signalben/Planar-Grasping-Platform/scara_CAD/endstops/amount.SLDPRT

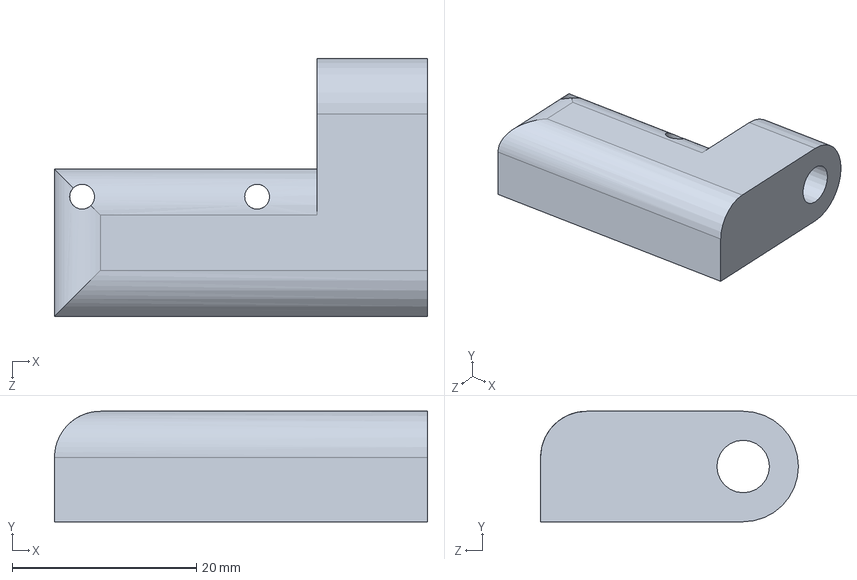
[picture p21: CAD file, 2021-09-22]
scara_CAD/endstops/amount.SLDPRT
40.5 x 12.0 x 28.0 mm
