signalben/Planar-Grasping-Platform/scara_CAD/gripper/top_plate2.SLDPRT

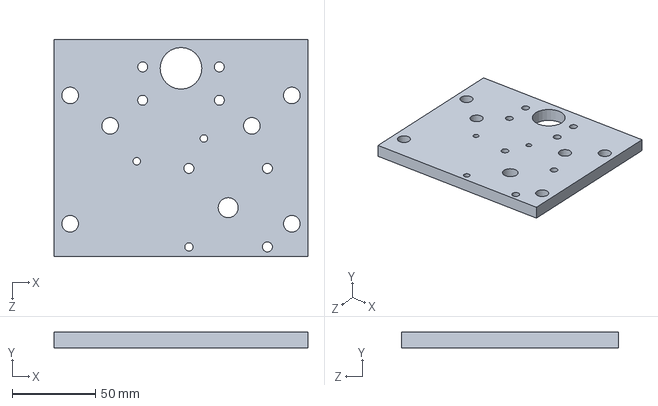
[picture p22: CAD file, 2021-09-22]
scara_CAD/gripper/top_plate2.SLDPRT
152.4 x 9.50 x 130.0 mm
