signalben/Planar-Grasping-Platform/scara_CAD/realsenseD415_mount/camera_end.SLDPRT

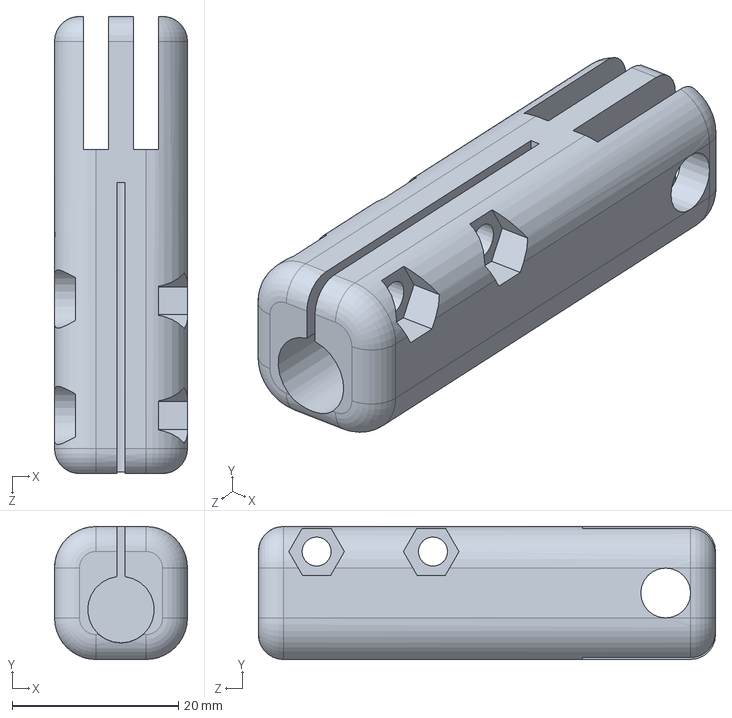
[picture p23: CAD file, 2021-09-22]
scara_CAD/realsenseD415_mount/camera_end.SLDPRT
16.0 x 16.0 x 55.0 mm
