signalben/Planar-Grasping-Platform/scara_ws/src/scara_description/ZL.STL

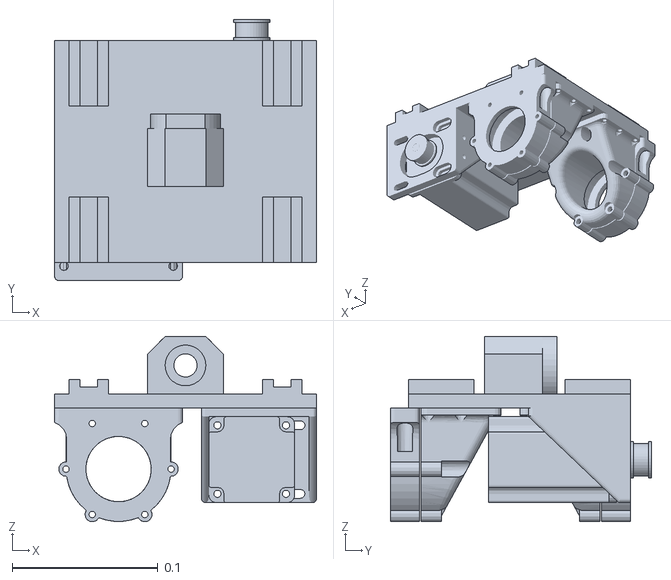
[picture p24: CAD file, 2021-09-26]
scara_ws/src/scara_description/ZL.STL
0.18 x 0.179 x 0.127
