signalben/Planar-Grasping-Platform/scara_CAD/controller/mega holder.SLDPRT

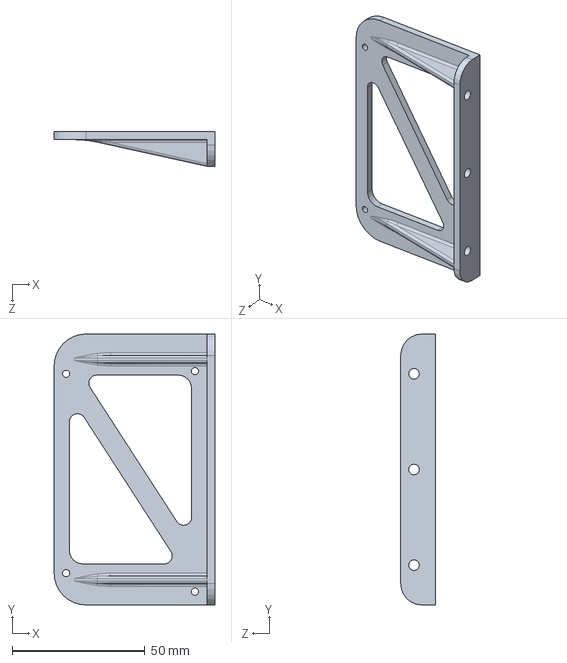
[picture p25: CAD file, 2021-09-22]
scara_CAD/controller/mega holder.SLDPRT
60.5 x 102.0 x 13.0 mm
