signalben/Planar-Grasping-Platform/scara_CAD/endstops/zmount#.SLDPRT

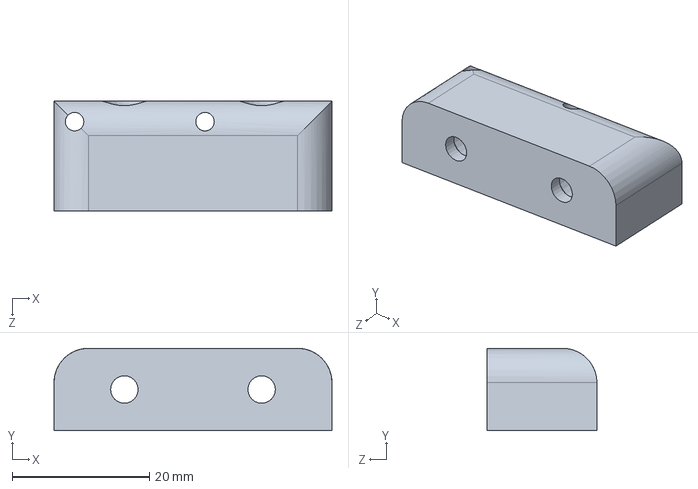
[picture p26: CAD file, 2021-09-22]
scara_CAD/endstops/zmount#.SLDPRT
40.5 x 12.0 x 16.0 mm
