signalben/Planar-Grasping-Platform/scara_CAD/gripper/motor.SLDPRT

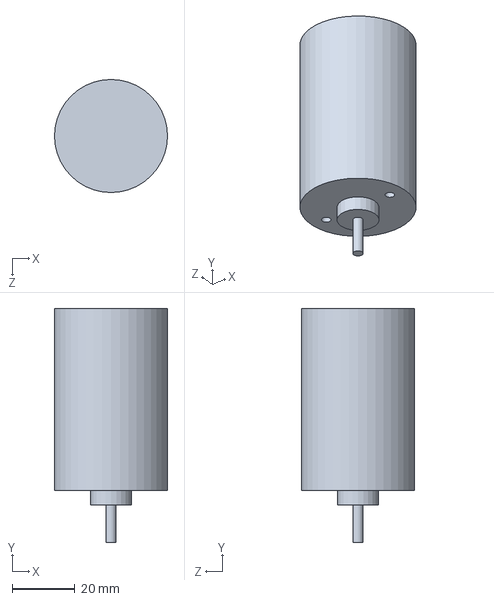
[picture p27: CAD file, 2021-09-22]
scara_CAD/gripper/motor.SLDPRT
36.0 x 74.5 x 36.0 mm
