signalben/Planar-Grasping-Platform/scara_CAD/manipulator/nema17_mount.SLDPRT

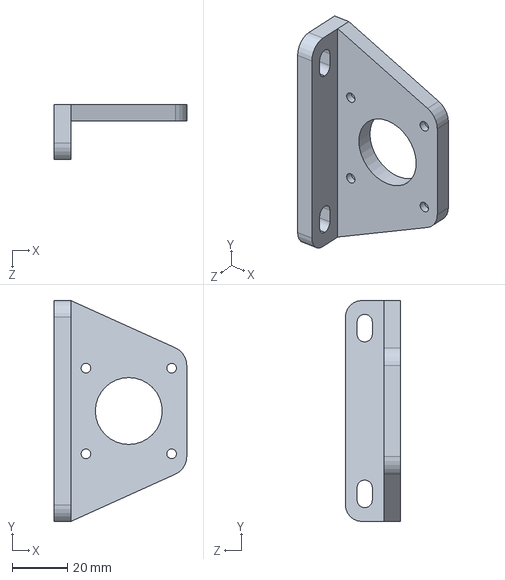
[picture p28: CAD file, 2021-09-22]
scara_CAD/manipulator/nema17_mount.SLDPRT
48.0 x 80.0 x 20.0 mm
