signalben/Planar-Grasping-Platform/scara_CAD/realsenseD415_mount/camera_rod.SLDPRT

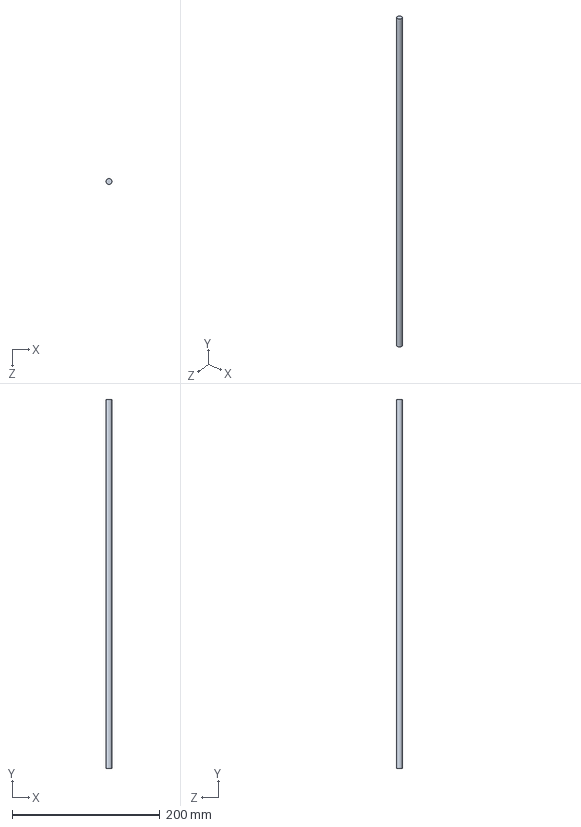
[picture p29: CAD file, 2021-09-22]
scara_CAD/realsenseD415_mount/camera_rod.SLDPRT
8.00 x 500.0 x 8.00 mm
