signalben/Planar-Grasping-Platform/scara_ws/src/scara_description/YL.STL

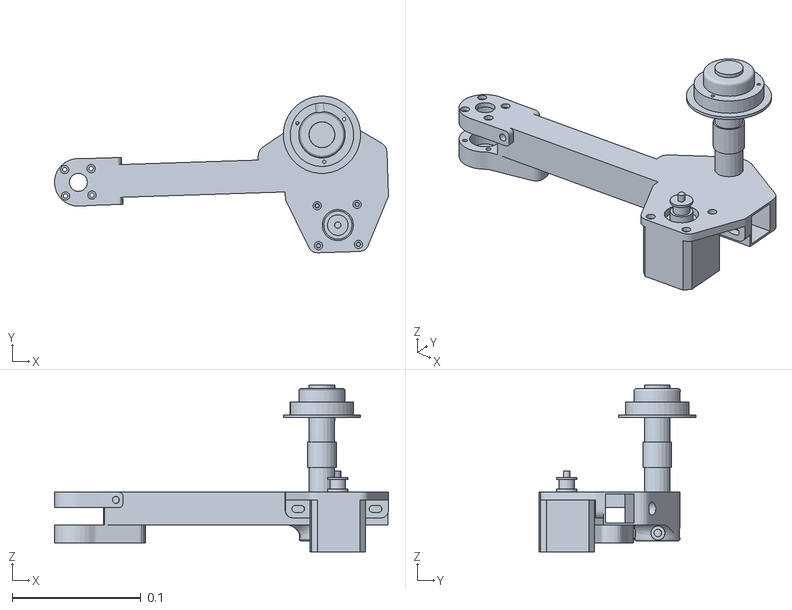
[picture p30: CAD file, 2021-09-26]
scara_ws/src/scara_description/YL.STL
0.259 x 0.121 x 0.129
