signalben/Planar-Grasping-Platform/scara_CAD/controller/fan_plate.SLDPRT

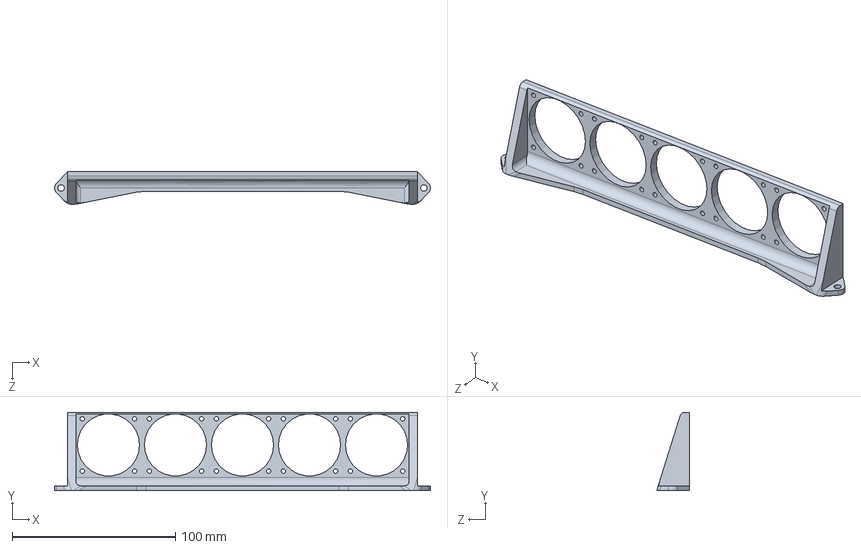
[picture p31: CAD file, 2021-09-22]
scara_CAD/controller/fan_plate.SLDPRT
230.0 x 48.0 x 20.0 mm
