signalben/Planar-Grasping-Platform/scara_CAD/endstops/amount2.SLDPRT

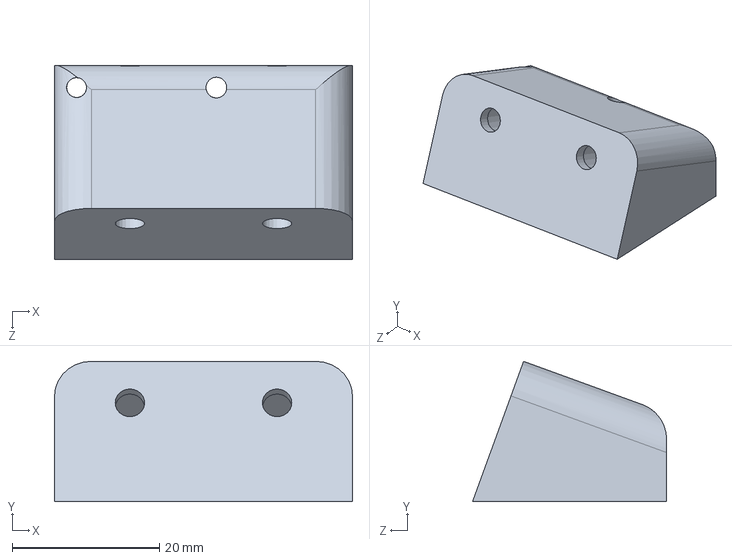
[picture p32: CAD file, 2021-09-22]
scara_CAD/endstops/amount2.SLDPRT
40.5 x 19.1 x 26.4 mm
