signalben/Planar-Grasping-Platform/scara_CAD/gripper/small_side_plate.SLDPRT

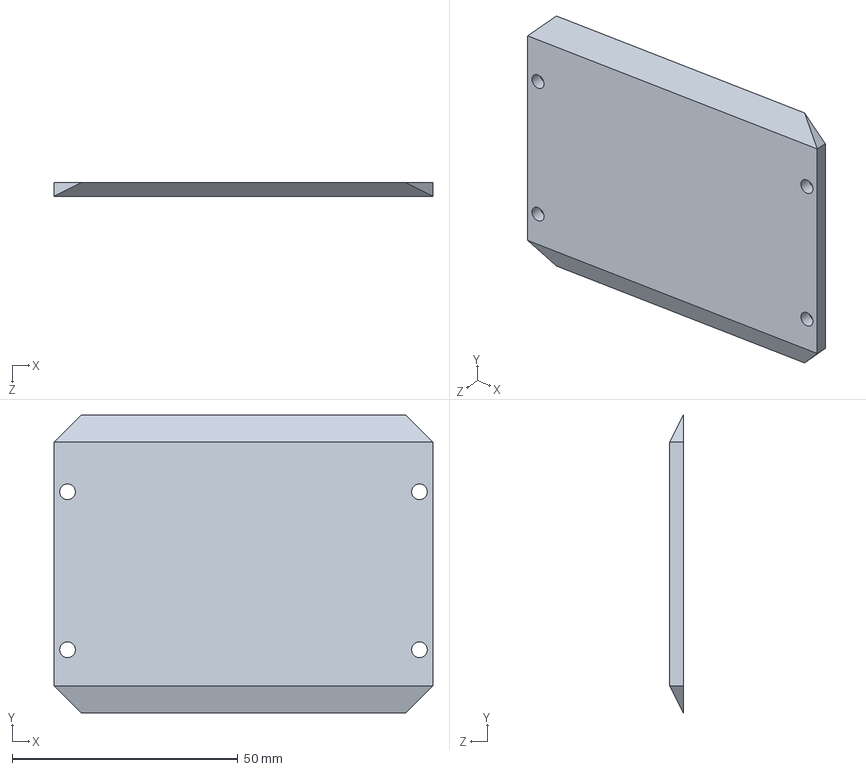
[picture p33: CAD file, 2021-09-22]
scara_CAD/gripper/small_side_plate.SLDPRT
84.0 x 66.0 x 3.00 mm
