signalben/Planar-Grasping-Platform/scara_CAD/manipulator/ballnut_holder.SLDPRT

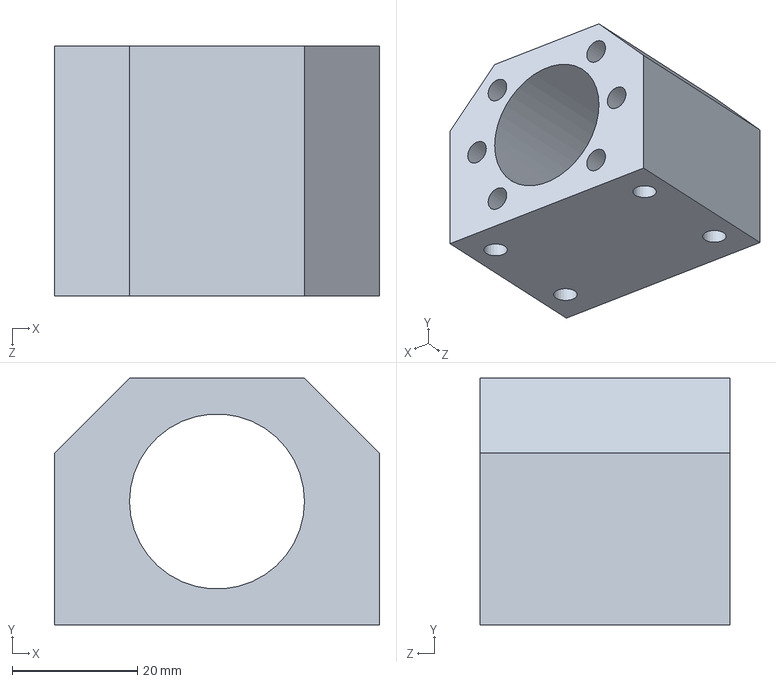
[picture p34: CAD file, 2021-09-22]
scara_CAD/manipulator/ballnut_holder.SLDPRT
52.0 x 39.5 x 40.0 mm
