signalben/Planar-Grasping-Platform/scara_ws/src/scara_description/jaw1.STL

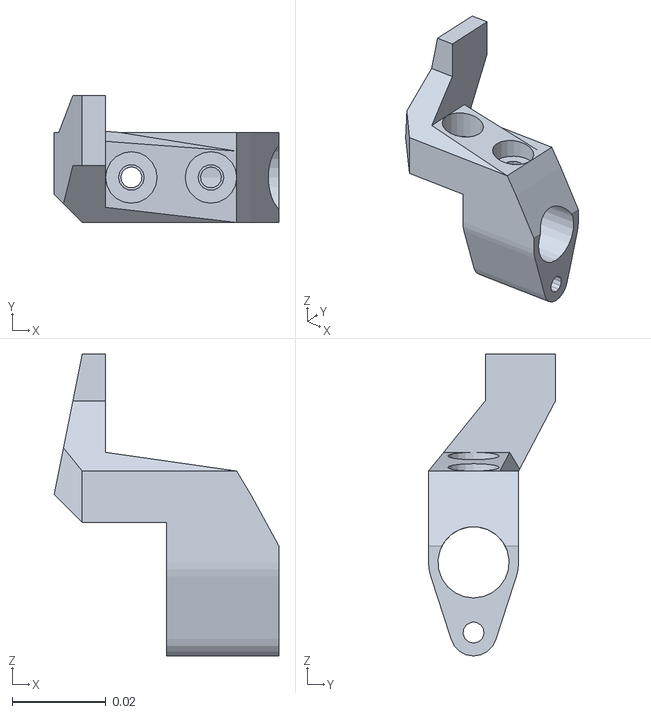
[picture p35: CAD file, 2021-09-26]
scara_ws/src/scara_description/jaw1.STL
0.048 x 0.0271 x 0.0645
