signalben/Planar-Grasping-Platform/scara_CAD/controller/clamp.SLDPRT

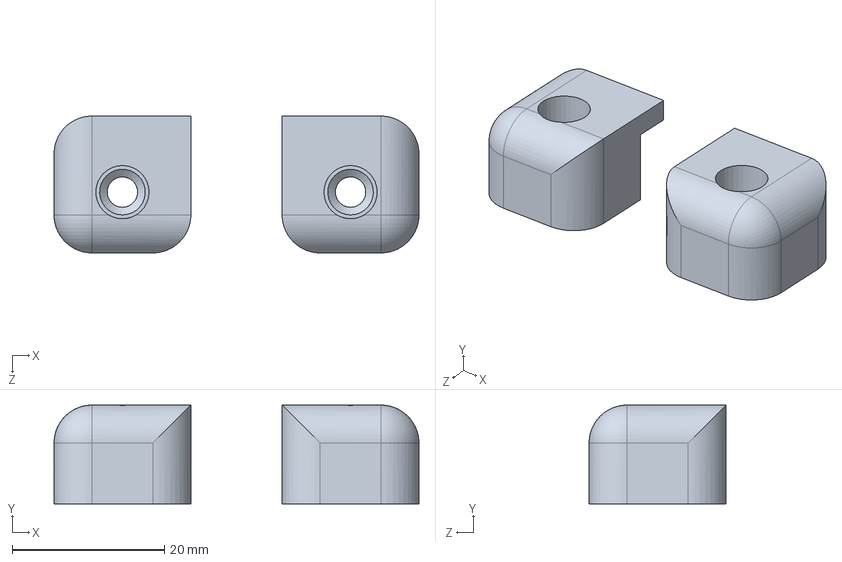
[picture p36: CAD file, 2021-09-22]
scara_CAD/controller/clamp.SLDPRT
48.0 x 13.0 x 18.0 mm
