signalben/Planar-Grasping-Platform/scara_CAD/endstops/bmount.SLDPRT

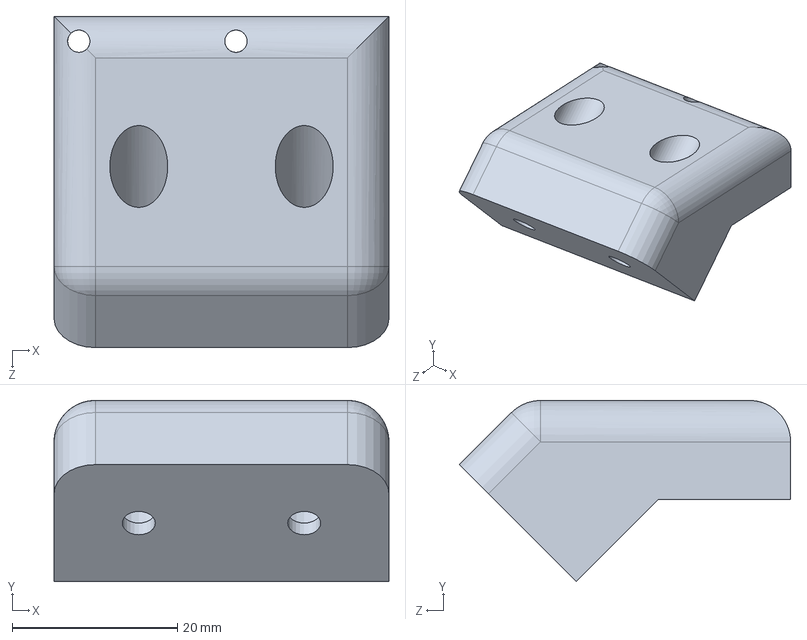
[picture p37: CAD file, 2021-09-22]
scara_CAD/endstops/bmount.SLDPRT
40.5 x 21.9 x 40.0 mm
