signalben/Planar-Grasping-Platform/scara_CAD/gripper/finger.SLDPRT

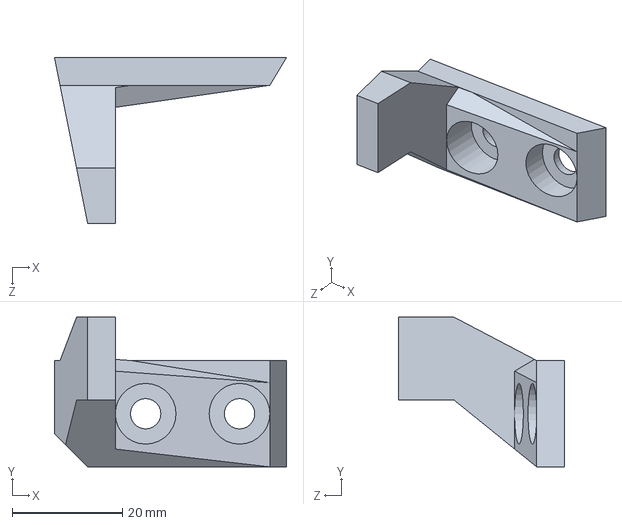
[picture p38: CAD file, 2021-09-22]
scara_CAD/gripper/finger.SLDPRT
42.0 x 27.1 x 30.0 mm
