signalben/Planar-Grasping-Platform/scara_CAD/manipulator/gt2_25t.SLDPRT

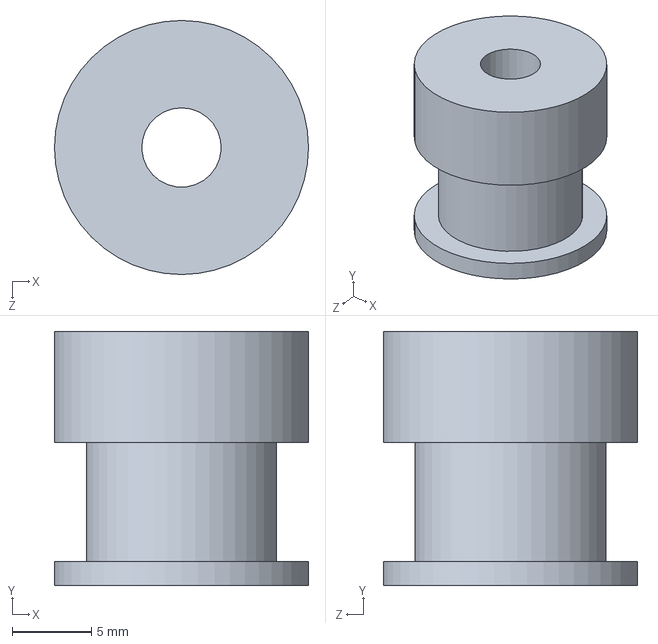
[picture p39: CAD file, 2021-09-22]
scara_CAD/manipulator/gt2_25t.SLDPRT
16.0 x 16.0 x 16.0 mm
