signalben/Planar-Grasping-Platform/scara_CAD/realsenseD415_mount/sidemount.SLDPRT

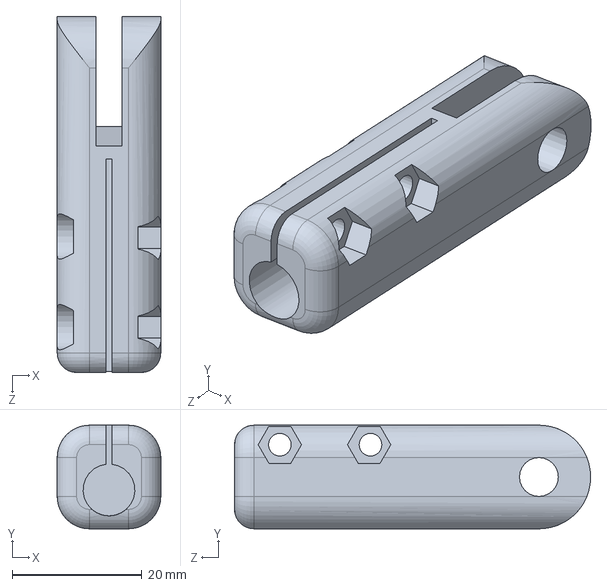
[picture p40: CAD file, 2021-09-22]
scara_CAD/realsenseD415_mount/sidemount.SLDPRT
16.0 x 16.0 x 55.0 mm
