signalben/Planar-Grasping-Platform/scara_ws/src/scara_description/XL.STL

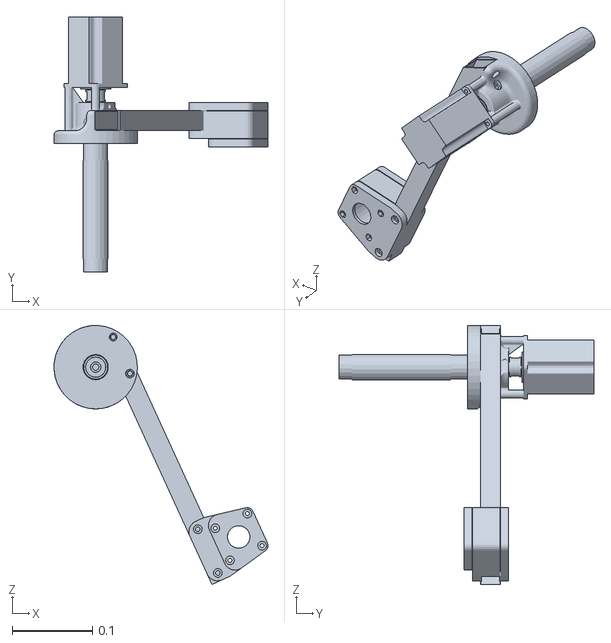
[picture p41: CAD file, 2021-09-26]
scara_ws/src/scara_description/XL.STL
0.267 x 0.317 x 0.323
