signalben/Planar-Grasping-Platform/scara_CAD/gripper/shell_no_motor.SLDPRT

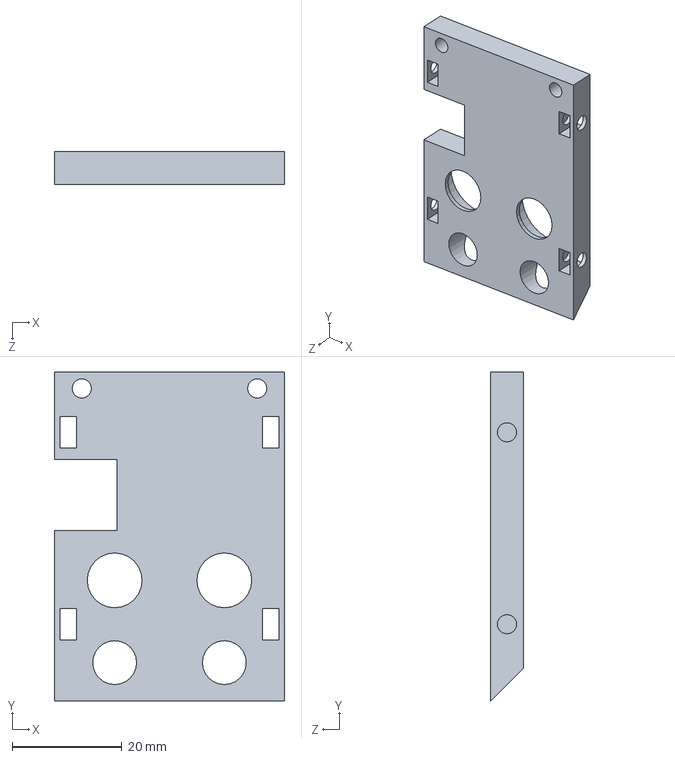
[picture p43: CAD file, 2021-09-22]
scara_CAD/gripper/shell_no_motor.SLDPRT
42.0 x 60.0 x 6.00 mm
