signalben/Planar-Grasping-Platform/scara_CAD/manipulator/side_plate.SLDPRT

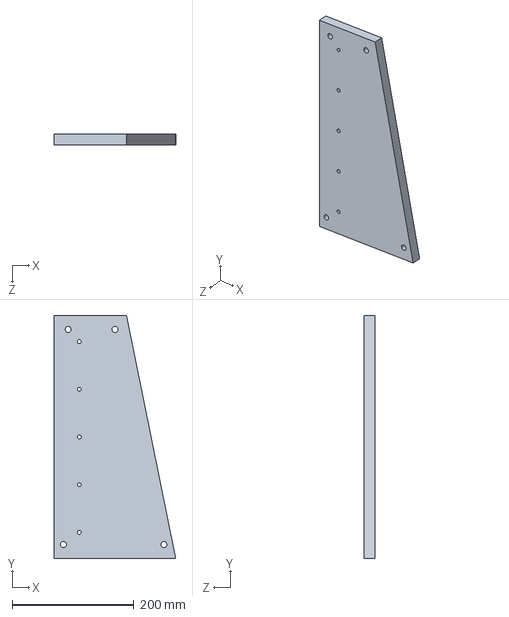
[picture p44: CAD file, 2021-09-22]
scara_CAD/manipulator/side_plate.SLDPRT
200.0 x 400.0 x 18.0 mm
