signalben/Planar-Grasping-Platform/scara_CAD/realsenseD415_mount/sidemount2.SLDPRT

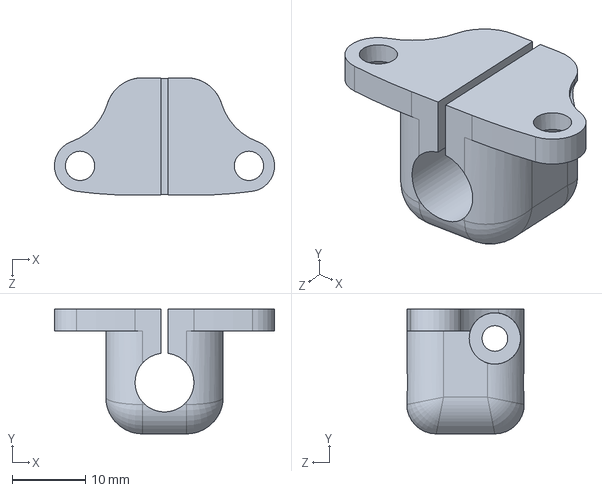
[picture p45: CAD file, 2021-09-22]
scara_CAD/realsenseD415_mount/sidemount2.SLDPRT
30.0 x 17.0 x 16.0 mm
