signalben/Planar-Grasping-Platform/scara_ws/src/scara_description/AL.STL

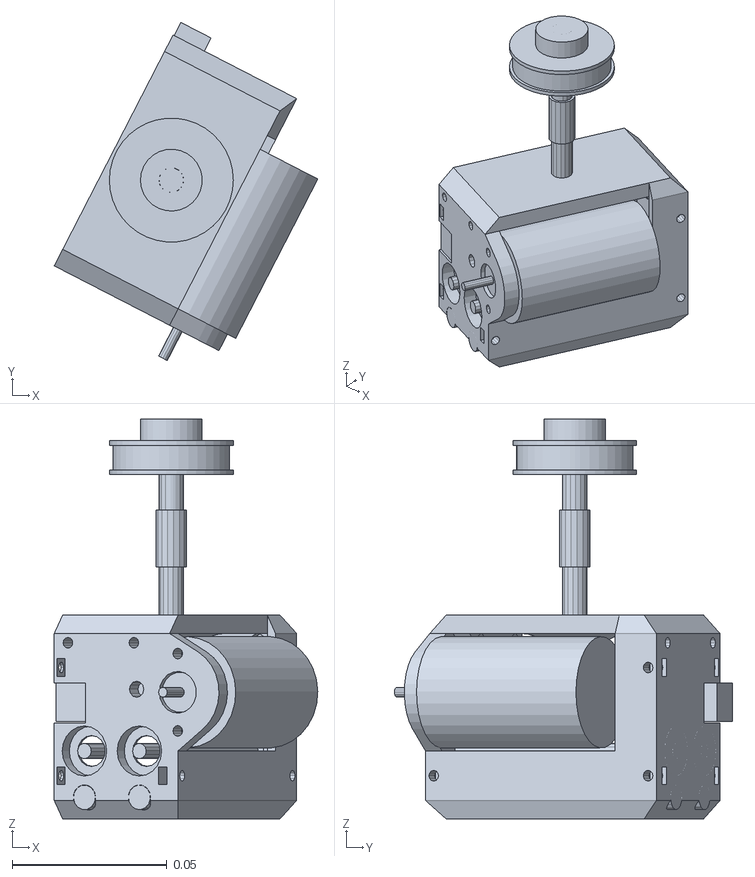
[picture p46: CAD file, 2021-09-26]
scara_ws/src/scara_description/AL.STL
0.0853 x 0.109 x 0.129
