signalben/Planar-Grasping-Platform/scara_CAD/gripper/mini_bearing.SLDPRT

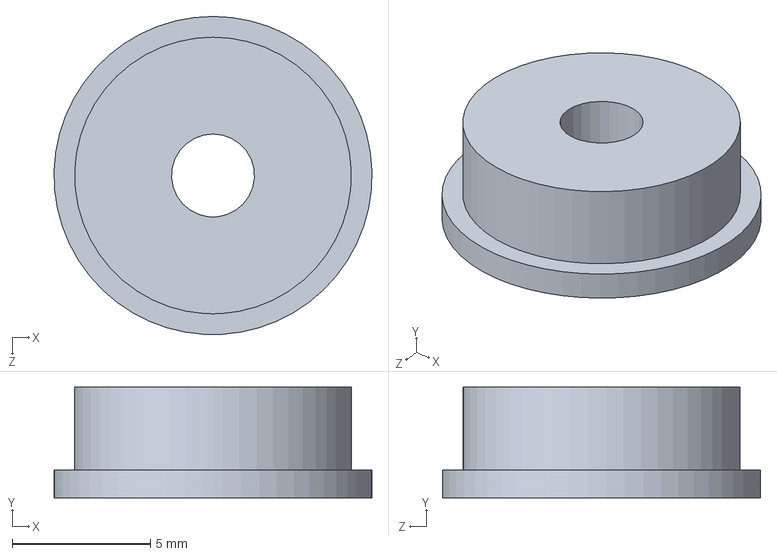
[picture p47: CAD file, 2021-09-22]
scara_CAD/gripper/mini_bearing.SLDPRT
11.5 x 4.00 x 11.5 mm
