signalben/Planar-Grasping-Platform/scara_CAD/manipulator/large_bearing.SLDPRT

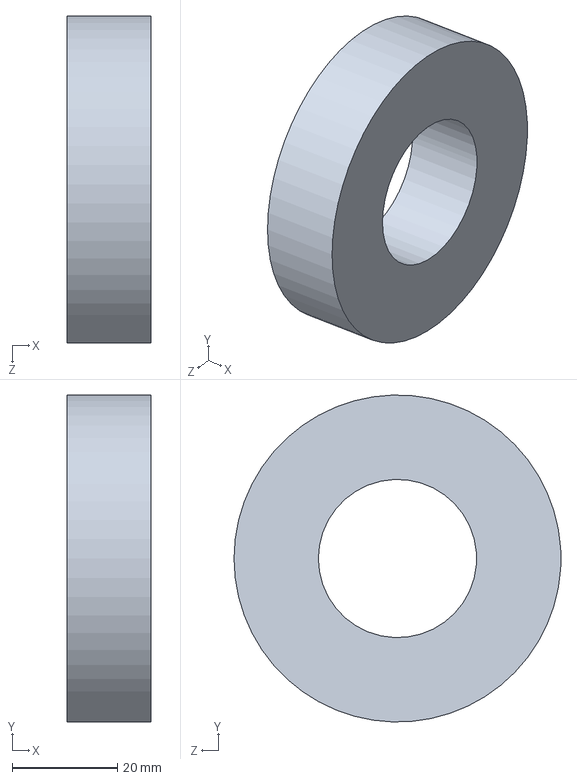
[picture p48: CAD file, 2021-09-22]
scara_CAD/manipulator/large_bearing.SLDPRT
16.0 x 62.0 x 62.0 mm
