signalben/Planar-Grasping-Platform/scara_CAD/gripper/gear1.SLDPRT

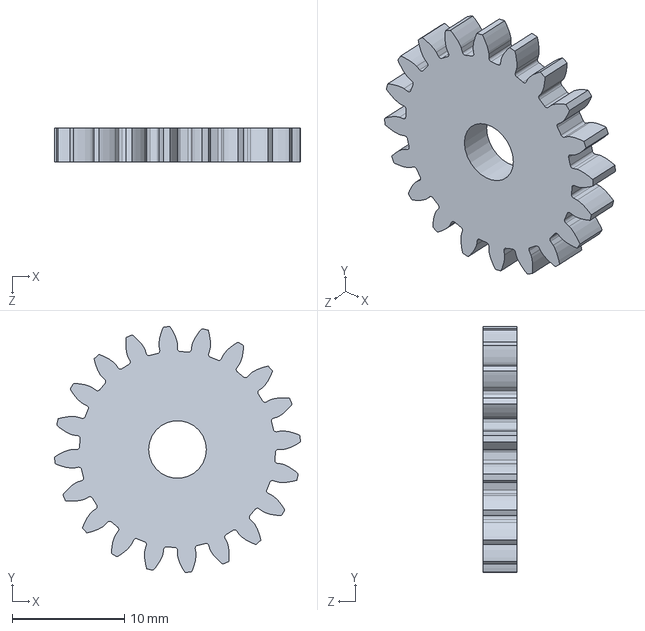
[picture p49: CAD file, 2021-09-22]
scara_CAD/gripper/gear1.SLDPRT
22.0 x 22.0 x 3.00 mm
