signalben/Planar-Grasping-Platform/scara_CAD/manipulator/new_tensioner.SLDPRT

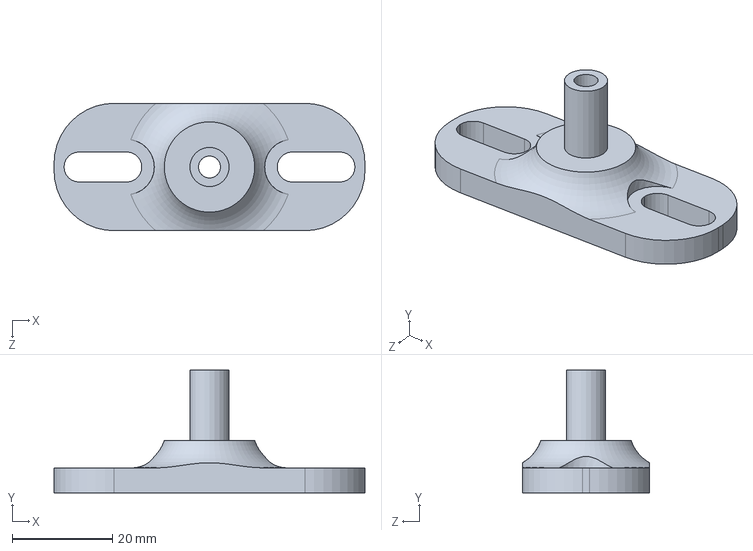
[picture p50: CAD file, 2021-09-22]
scara_CAD/manipulator/new_tensioner.SLDPRT
62.0 x 24.5 x 25.4 mm
