signalben/Planar-Grasping-Platform/scara_CAD/gripper/potentiomer.SLDPRT

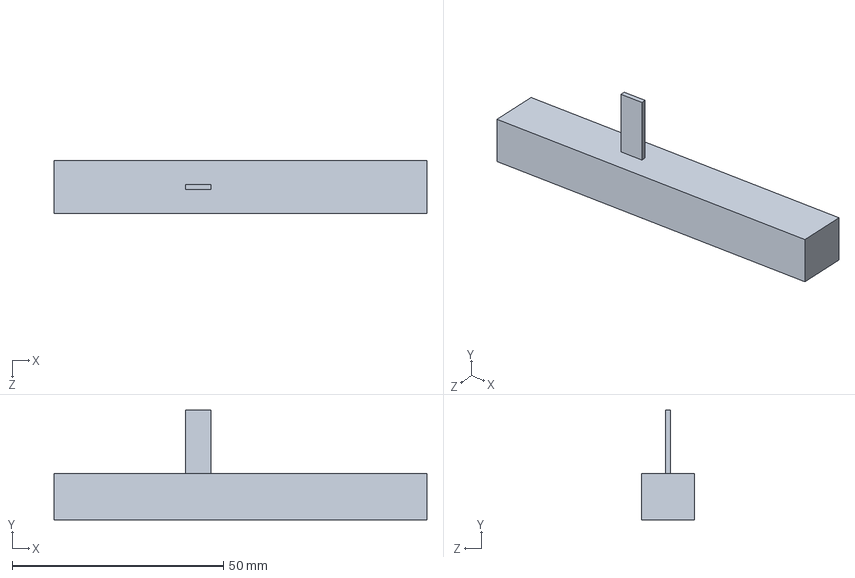
[picture p51: CAD file, 2021-09-22]
scara_CAD/gripper/potentiomer.SLDPRT
88.2 x 26.0 x 12.5 mm
