signalben/Planar-Grasping-Platform/scara_CAD/manipulator/j2_tensioner.SLDPRT

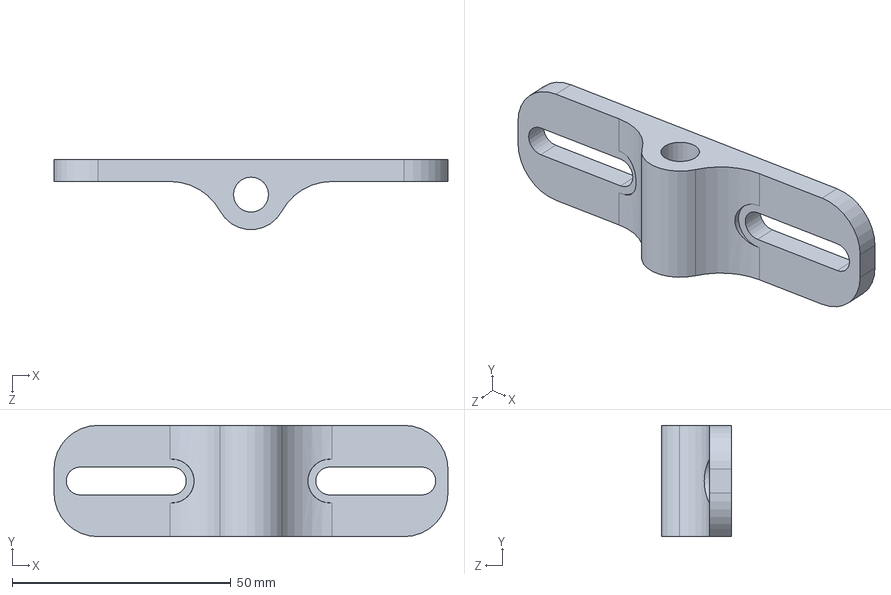
[picture p52: CAD file, 2021-09-22]
scara_CAD/manipulator/j2_tensioner.SLDPRT
90.0 x 25.4 x 15.9 mm
