signalben/Planar-Grasping-Platform/scara_CAD/gripper/skate_bearing2.SLDPRT

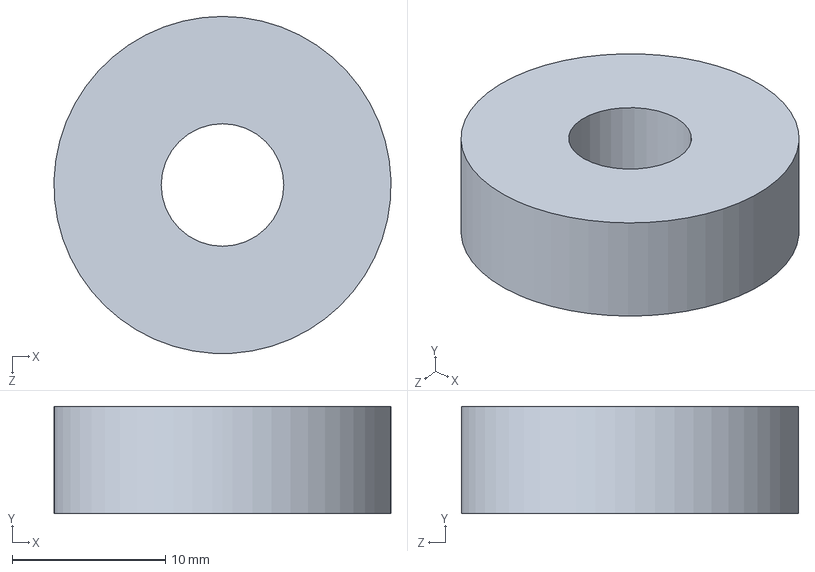
[picture p53: CAD file, 2021-09-22]
scara_CAD/gripper/skate_bearing2.SLDPRT
22.0 x 7.00 x 22.0 mm
