signalben/Planar-Grasping-Platform/scara_CAD/manipulator/back_plate.SLDPRT

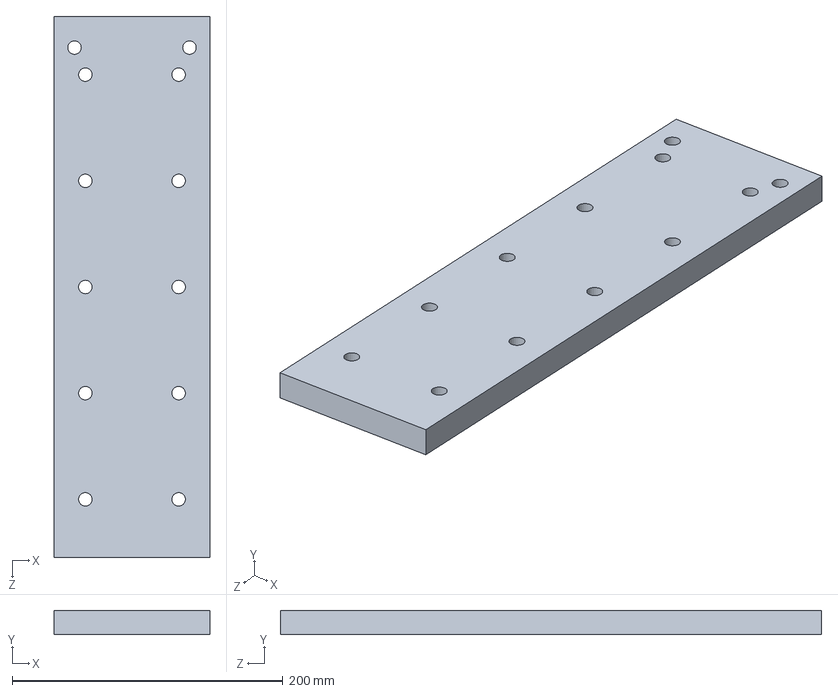
[picture p54: CAD file, 2021-09-22]
scara_CAD/manipulator/back_plate.SLDPRT
115.0 x 18.0 x 400.0 mm
