signalben/Planar-Grasping-Platform/scara_CAD/gripper/shell.SLDPRT

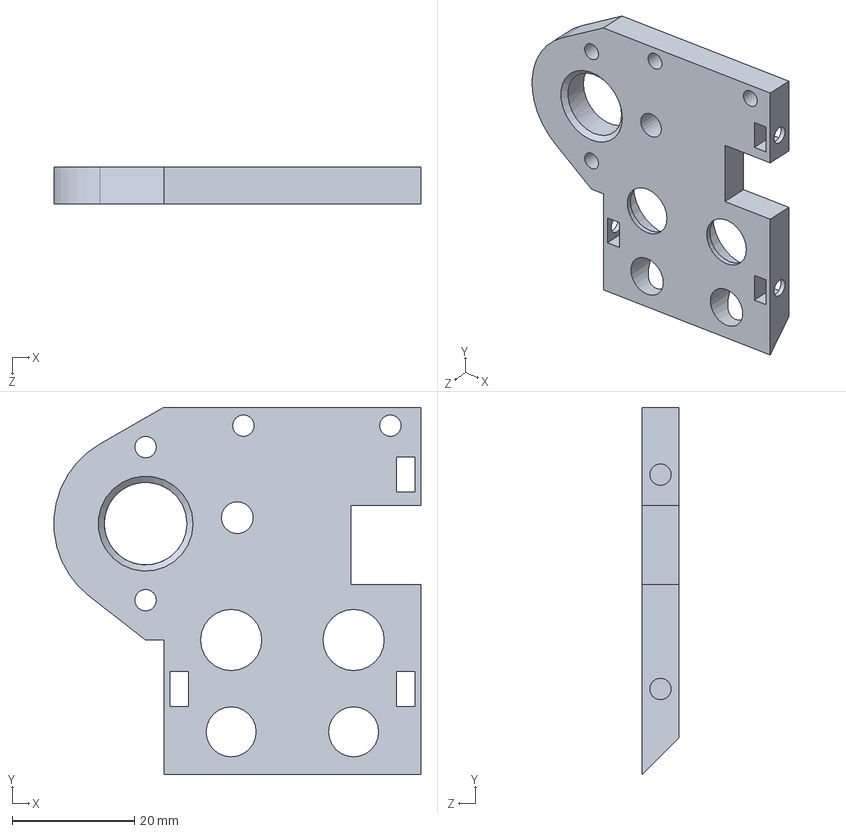
[picture p55: CAD file, 2021-09-22]
scara_CAD/gripper/shell.SLDPRT
59.9 x 60.0 x 6.00 mm
