signalben/Planar-Grasping-Platform/scara_CAD/manipulator/z_motor_mount.SLDPRT

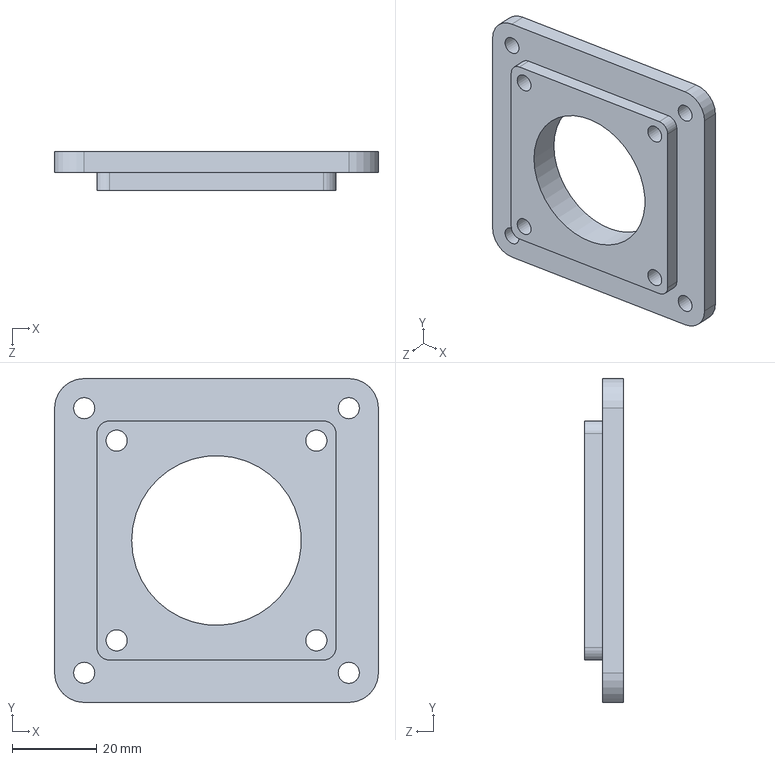
[picture p56: CAD file, 2021-09-22]
scara_CAD/manipulator/z_motor_mount.SLDPRT
76.4 x 76.4 x 9.20 mm
