signalben/Planar-Grasping-Platform/scara_CAD/gripper/rod.SLDPRT

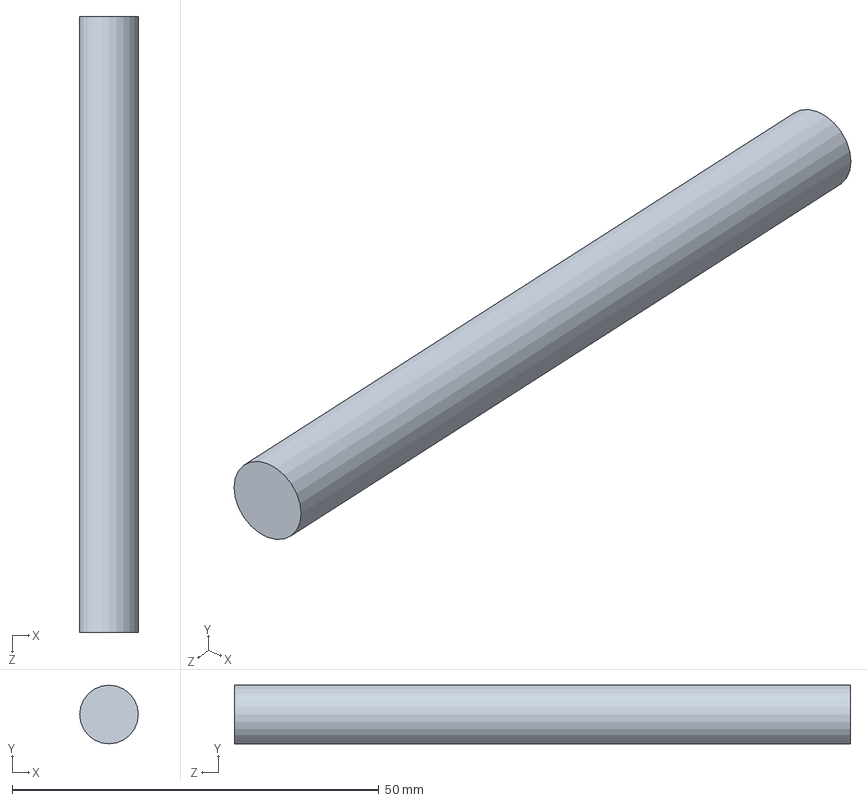
[picture p57: CAD file, 2021-09-22]
scara_CAD/gripper/rod.SLDPRT
8.00 x 8.00 x 84.0 mm
