signalben/Planar-Grasping-Platform/scara_CAD/manipulator/new2_tensioner.SLDPRT

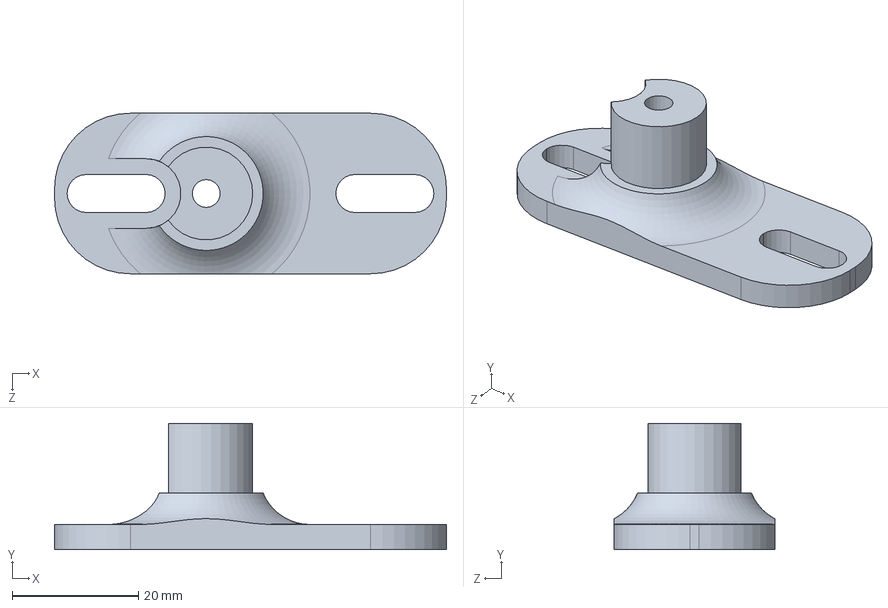
[picture p58: CAD file, 2021-09-22]
scara_CAD/manipulator/new2_tensioner.SLDPRT
62.0 x 20.0 x 25.4 mm
