signalben/Planar-Grasping-Platform/scara_CAD/gripper/mgear.SLDPRT

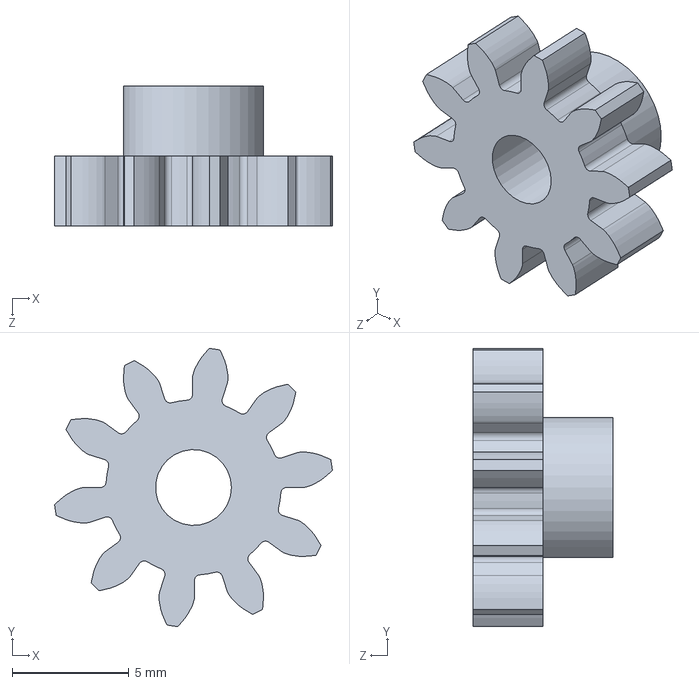
[picture p59: CAD file, 2021-09-22]
scara_CAD/gripper/mgear.SLDPRT
11.9 x 11.9 x 6.00 mm
