signalben/Planar-Grasping-Platform/scara_CAD/gripper/igear.SLDPRT

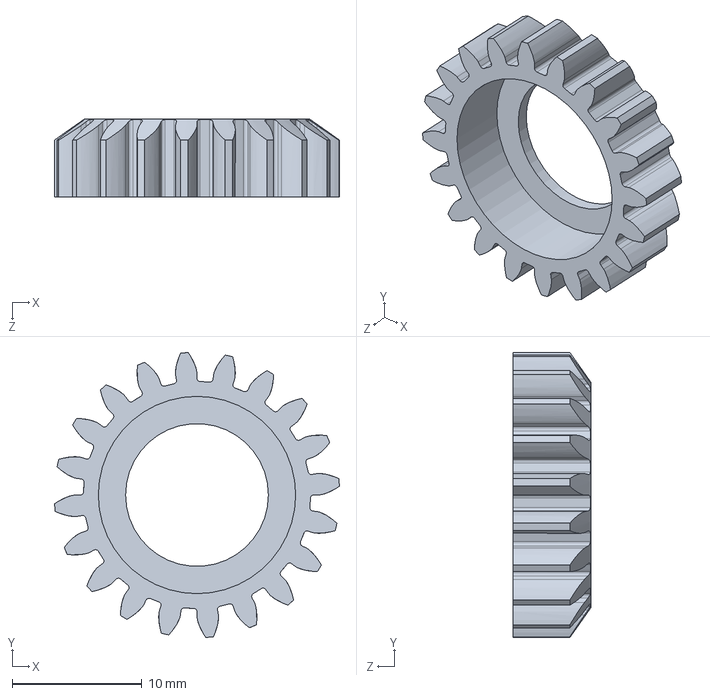
[picture p60: CAD file, 2021-09-22]
scara_CAD/gripper/igear.SLDPRT
22.0 x 22.0 x 6.00 mm
