signalben/Planar-Grasping-Platform/scara_CAD/manipulator/motot_mount_1.SLDPRT

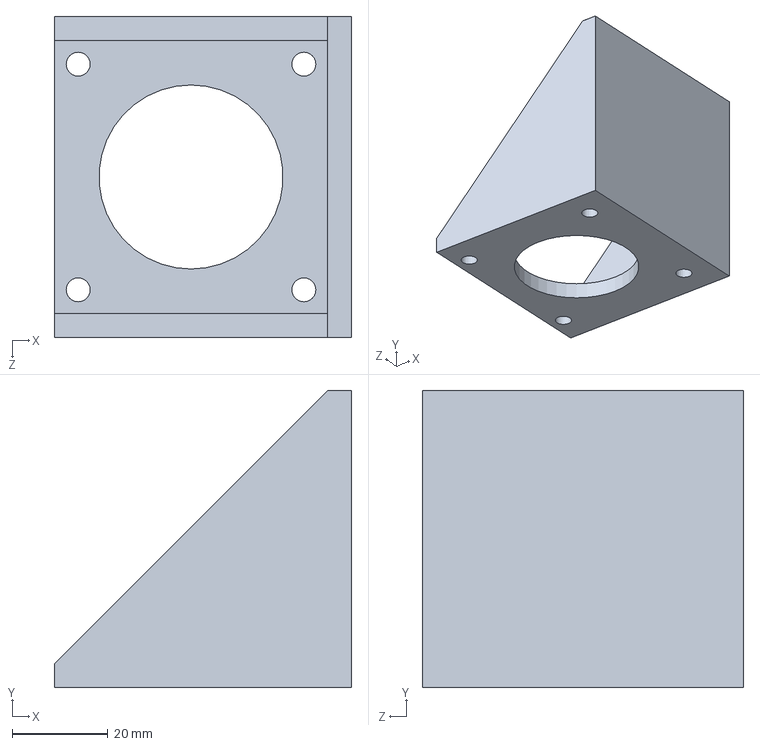
[picture p62: CAD file, 2021-09-22]
scara_CAD/manipulator/motot_mount_1.SLDPRT
62.0 x 62.0 x 67.0 mm
