signalben/Planar-Grasping-Platform/scara_CAD/manipulator/htd-22-15.SLDPRT

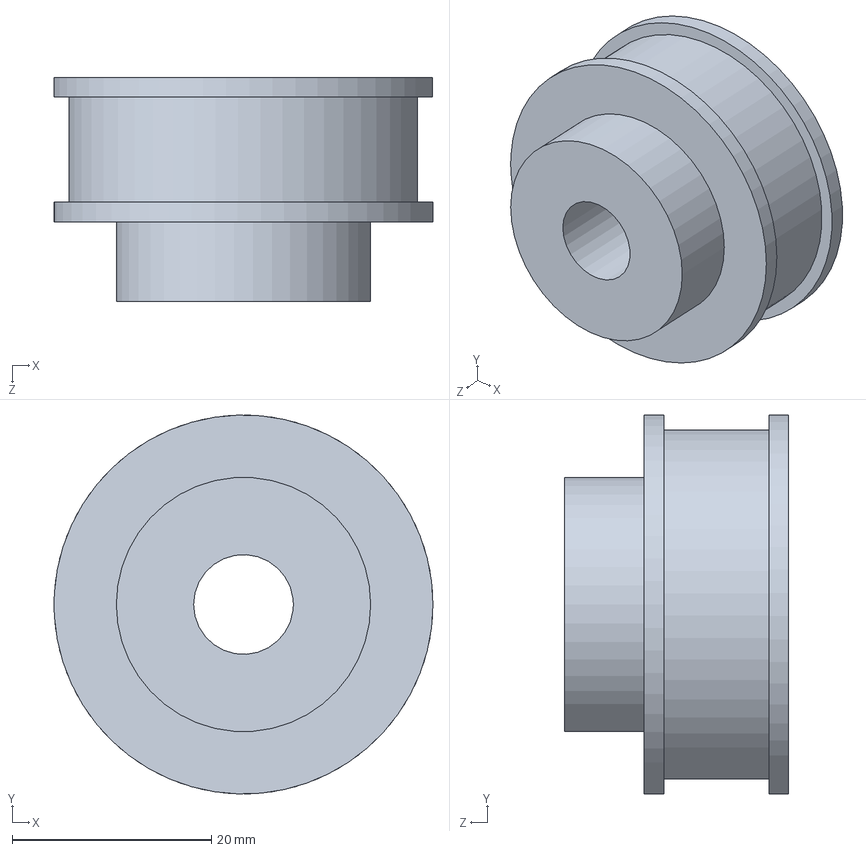
[picture p63: CAD file, 2021-09-22]
scara_CAD/manipulator/htd-22-15.SLDPRT
38.0 x 38.0 x 22.5 mm
