signalben/Planar-Grasping-Platform/scara_CAD/gripper/jaw.SLDPRT

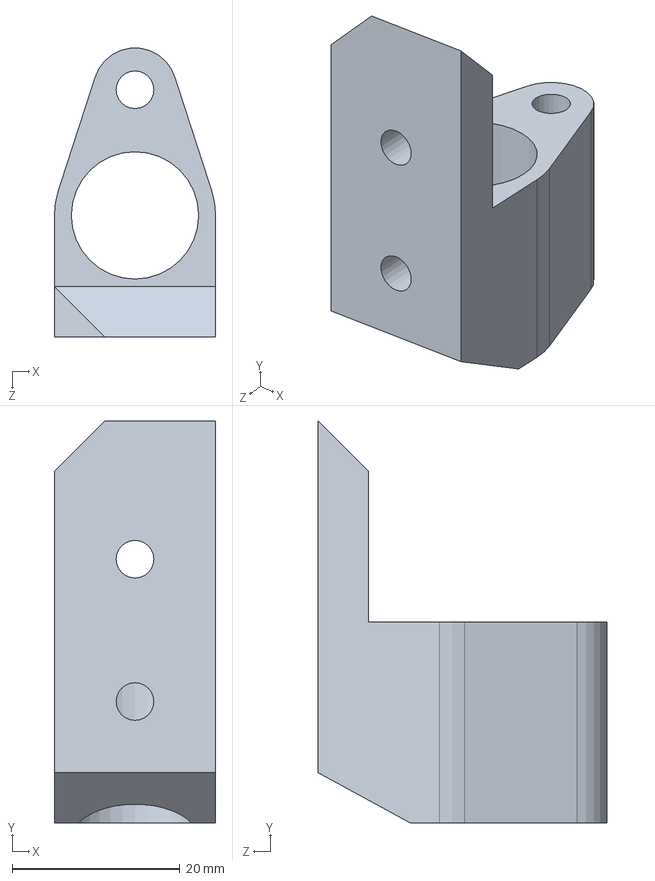
[picture p64: CAD file, 2021-09-22]
scara_CAD/gripper/jaw.SLDPRT
19.2 x 48.0 x 34.5 mm
