signalben/Planar-Grasping-Platform/scara_CAD/gripper/bearing6mm.SLDPRT

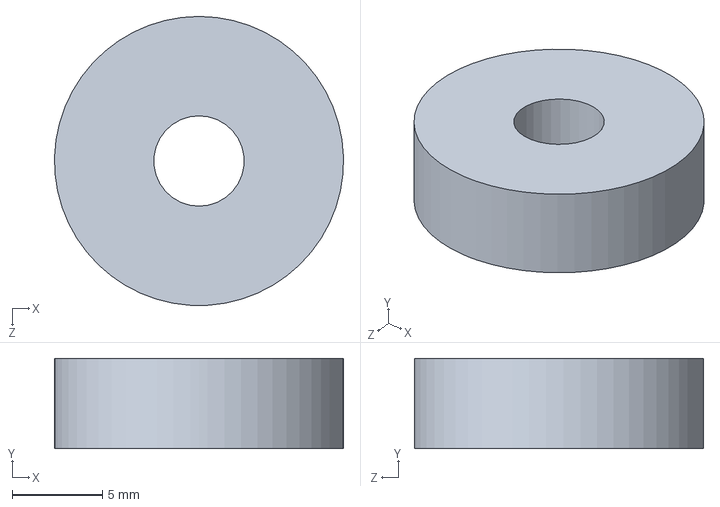
[picture p65: CAD file, 2021-09-22]
scara_CAD/gripper/bearing6mm.SLDPRT
16.0 x 5.00 x 16.0 mm
