signalben/Planar-Grasping-Platform/scara_CAD/gripper/top.SLDPRT

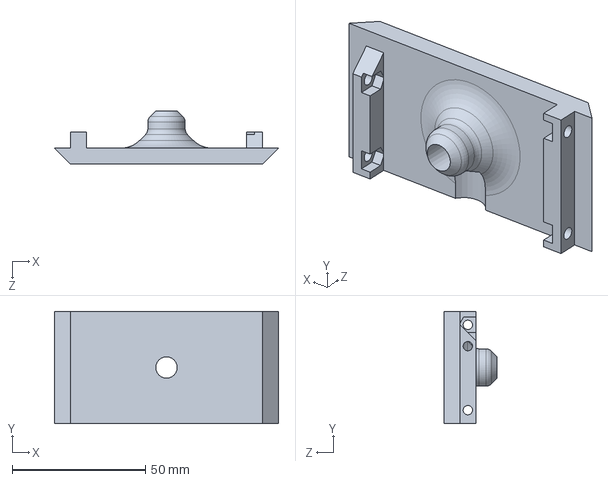
[picture p66: CAD file, 2021-09-22]
scara_CAD/gripper/top.SLDPRT
84.0 x 42.0 x 20.0 mm
