signalben/Planar-Grasping-Platform/scara_CAD/manipulator/joint2.SLDPRT

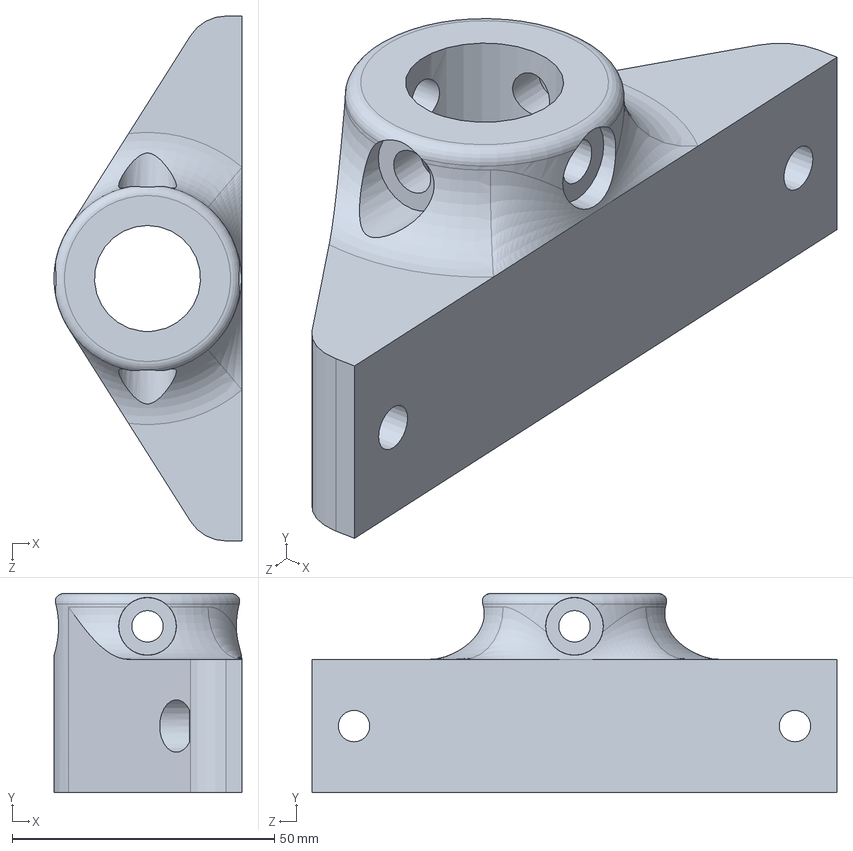
[picture p67: CAD file, 2021-09-22]
scara_CAD/manipulator/joint2.SLDPRT
35.8 x 38.0 x 100.0 mm
