signalben/Planar-Grasping-Platform/scara_CAD/gripper/linear_bearing.SLDPRT

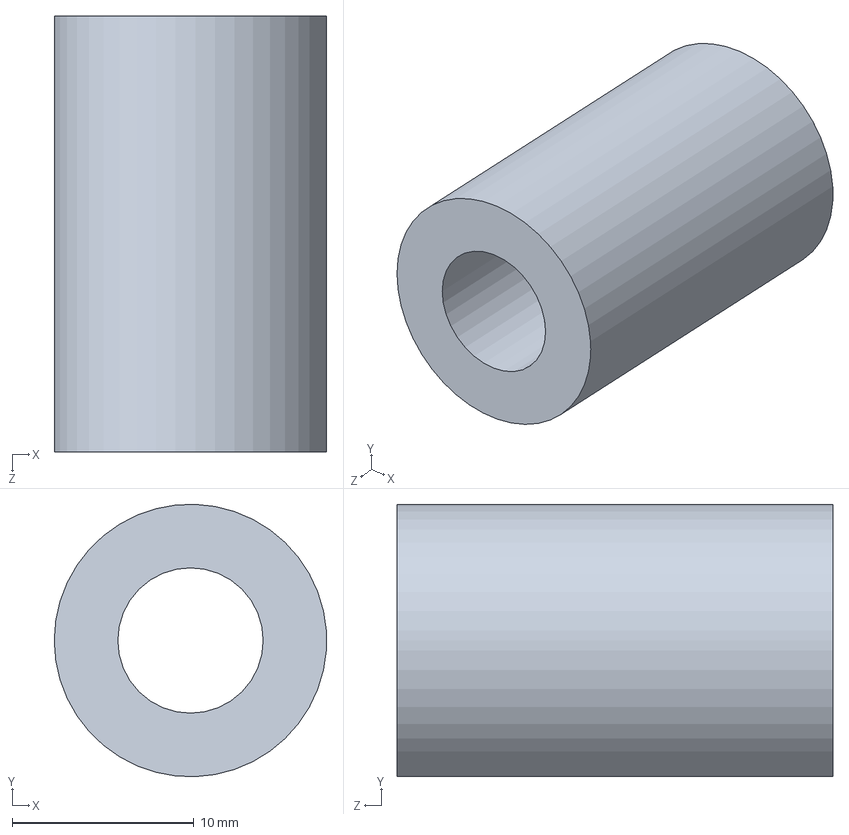
[picture p68: CAD file, 2021-09-22]
scara_CAD/gripper/linear_bearing.SLDPRT
15.0 x 15.0 x 24.0 mm
