signalben/Planar-Grasping-Platform/scara_CAD/gripper/jaw_potentiomer.SLDPRT

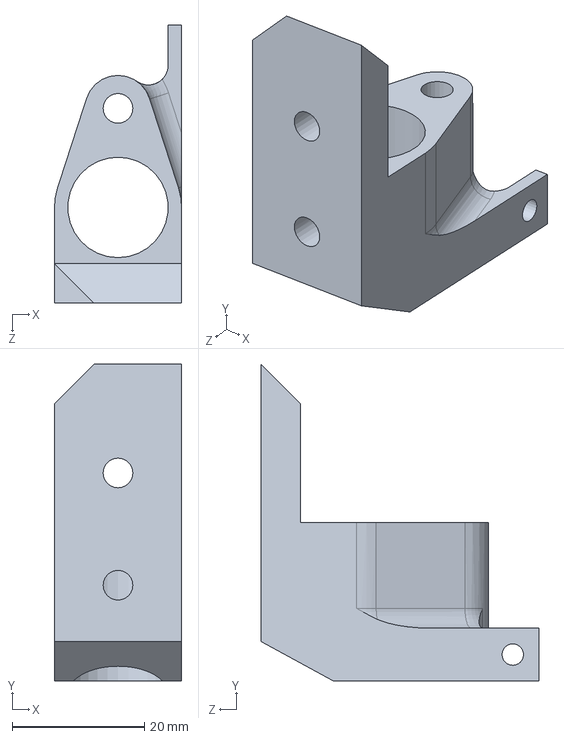
[picture p69: CAD file, 2021-09-22]
scara_CAD/gripper/jaw_potentiomer.SLDPRT
19.2 x 48.0 x 42.2 mm
