signalben/Planar-Grasping-Platform/scara_CAD/manipulator/j2_clamp.SLDPRT

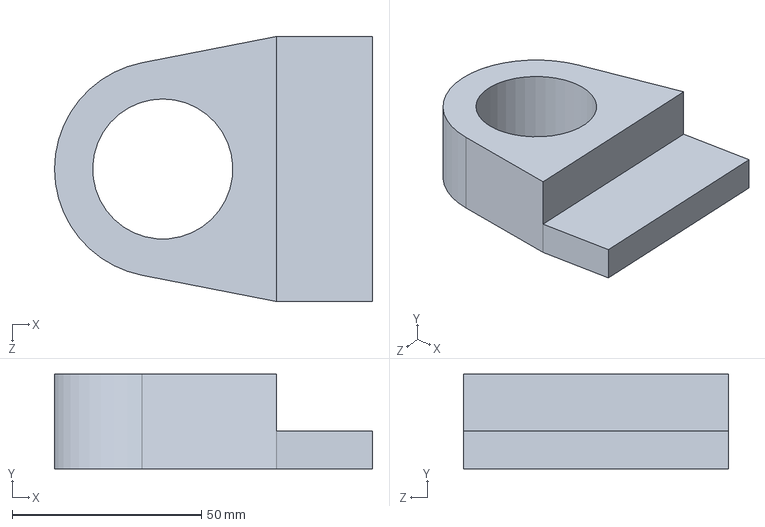
[picture p70: CAD file, 2021-09-22]
scara_CAD/manipulator/j2_clamp.SLDPRT
84.0 x 25.0 x 70.0 mm
