signalben/Planar-Grasping-Platform/scara_CAD/manipulator/j3bottomnew.SLDPRT

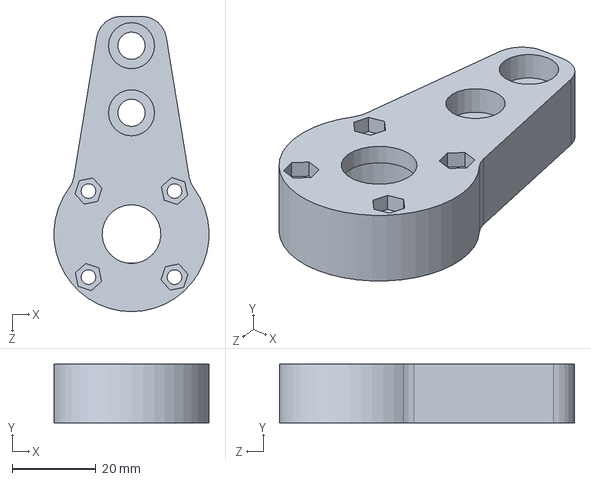
[picture p71: CAD file, 2021-09-22]
scara_CAD/manipulator/j3bottomnew.SLDPRT
37.0 x 14.0 x 70.4 mm
