signalben/Planar-Grasping-Platform/scara_CAD/manipulator/gt2_60t.SLDPRT

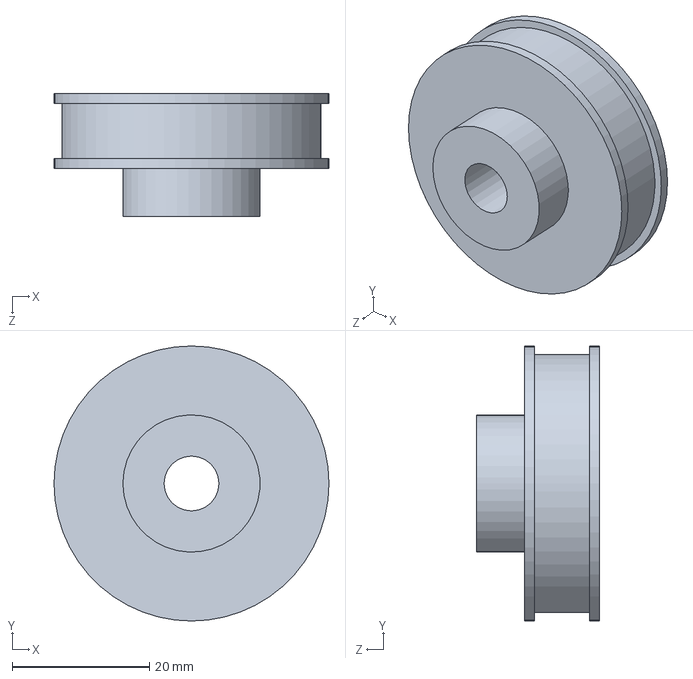
[picture p72: CAD file, 2021-09-22]
scara_CAD/manipulator/gt2_60t.SLDPRT
40.1 x 40.1 x 18.0 mm
