signalben/Planar-Grasping-Platform/scara_CAD/manipulator/mount_plate.SLDPRT

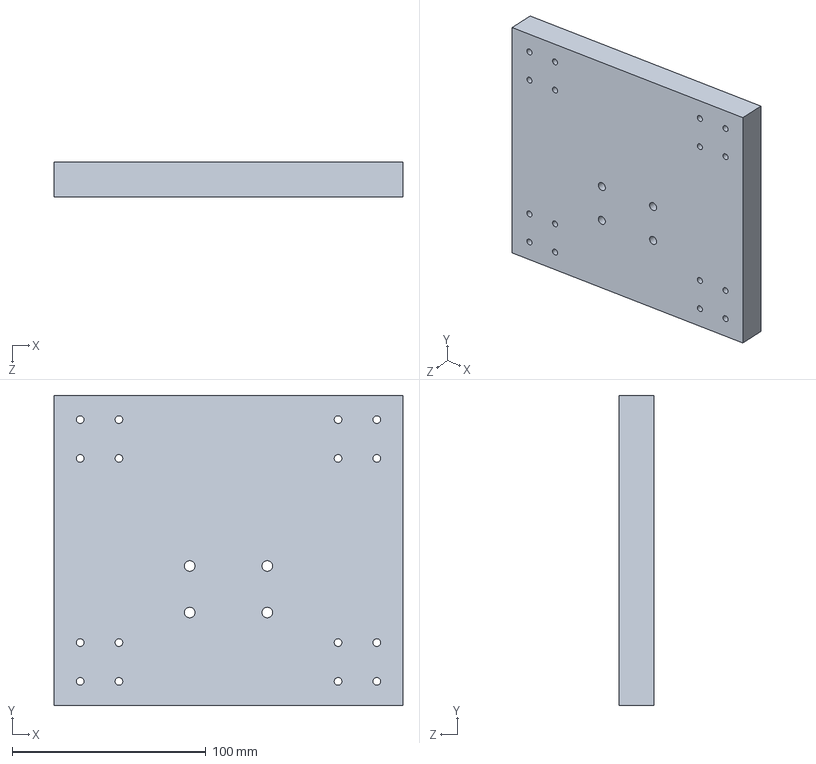
[picture p73: CAD file, 2021-09-22]
scara_CAD/manipulator/mount_plate.SLDPRT
180.0 x 160.0 x 18.0 mm
