signalben/Planar-Grasping-Platform/scara_CAD/manipulator/spacer.SLDPRT

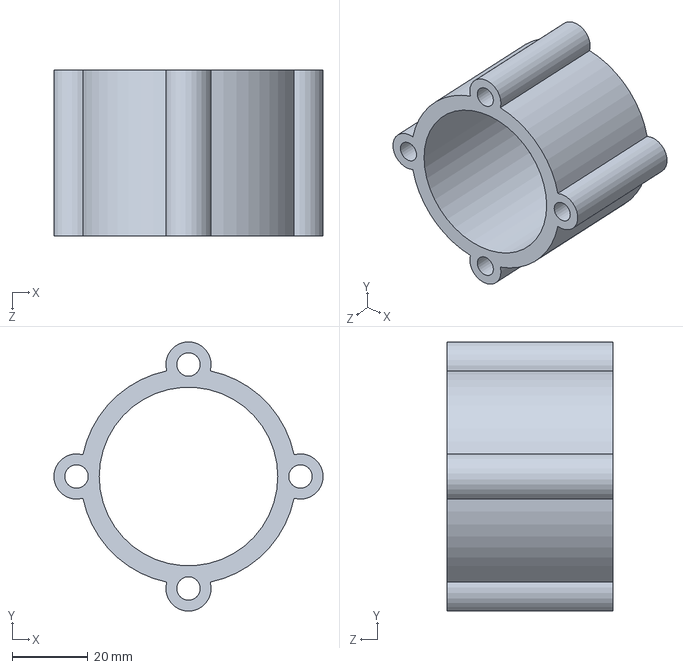
[picture p74: CAD file, 2021-09-22]
scara_CAD/manipulator/spacer.SLDPRT
71.1 x 71.1 x 44.0 mm
