signalben/Planar-Grasping-Platform/scara_CAD/manipulator/frame.SLDPRT

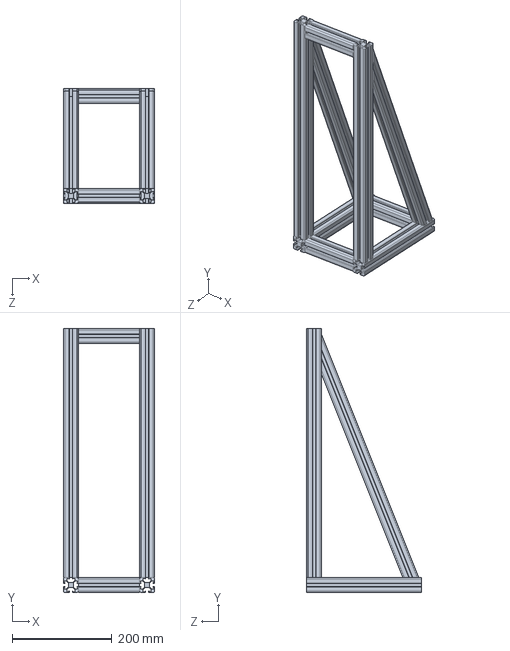
[picture p75: CAD file, 2021-09-22]
scara_CAD/manipulator/frame.SLDPRT
183.0 x 530.0 x 230.0 mm
