signalben/Planar-Grasping-Platform/scara_CAD/manipulator/clamp1.SLDPRT

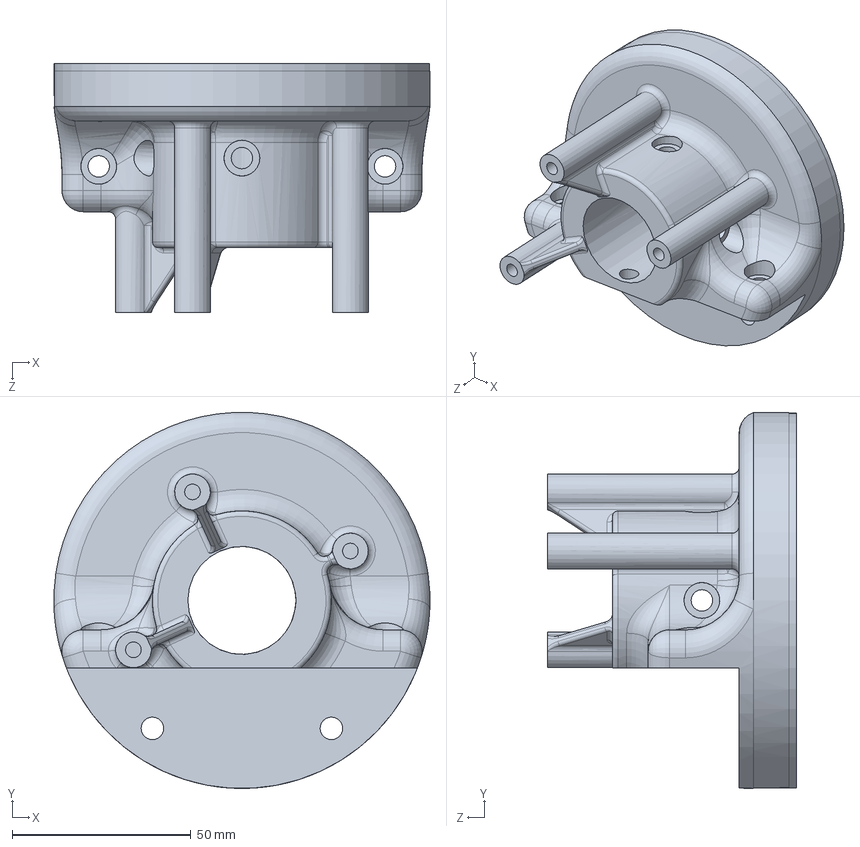
[picture p76: CAD file, 2021-09-22]
scara_CAD/manipulator/clamp1.SLDPRT
105.0 x 105.1 x 69.5 mm
