signalben/Planar-Grasping-Platform/scara_CAD/manipulator/medium_bearing.SLDPRT

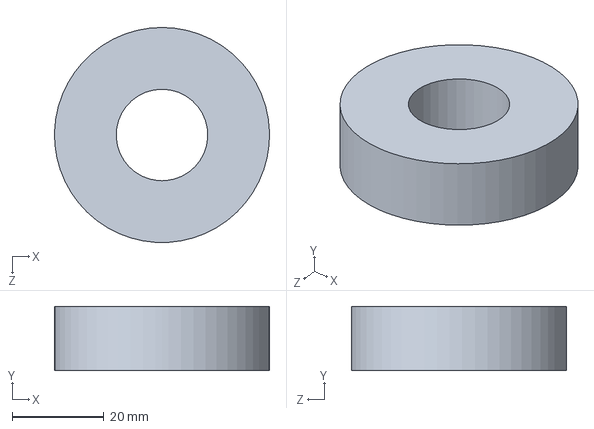
[picture p77: CAD file, 2021-09-22]
scara_CAD/manipulator/medium_bearing.SLDPRT
47.0 x 14.0 x 47.0 mm
