signalben/Planar-Grasping-Platform/scara_CAD/manipulator/nema17.SLDPRT

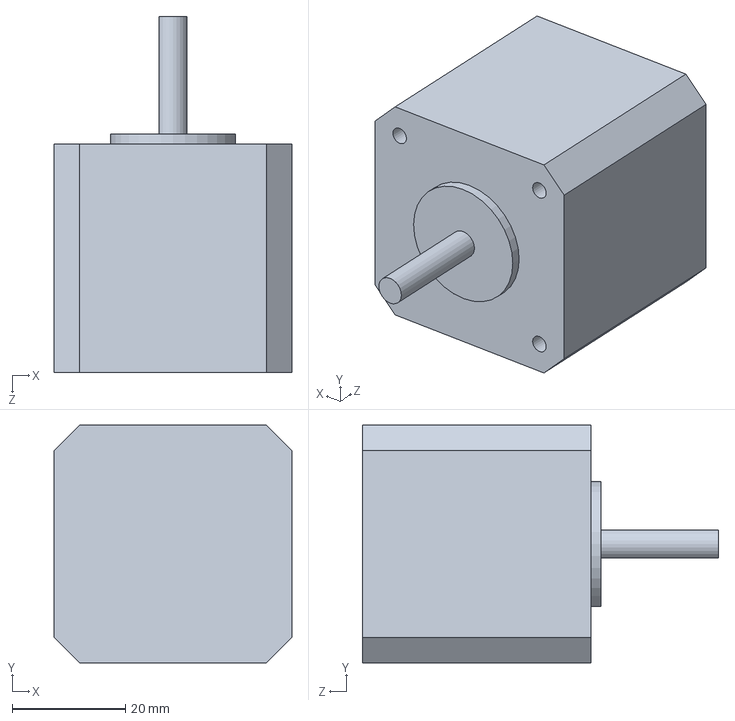
[picture p78: CAD file, 2021-09-22]
scara_CAD/manipulator/nema17.SLDPRT
42.0 x 42.0 x 62.8 mm
