signalben/Planar-Grasping-Platform/scara_CAD/manipulator/35t_htd.SLDPRT

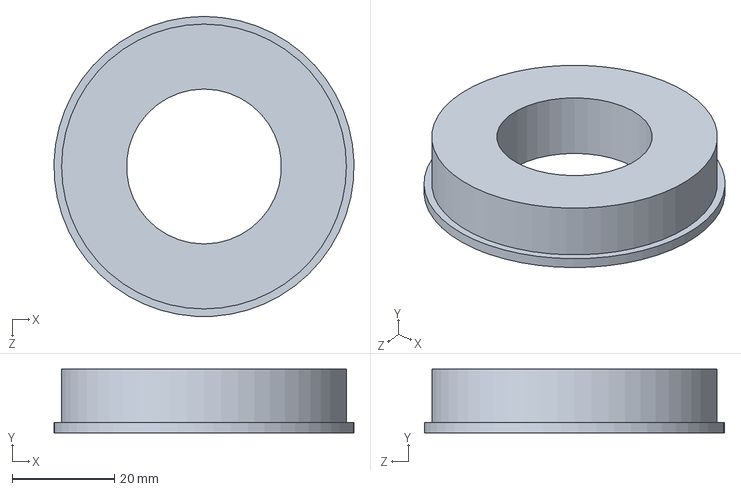
[picture p79: CAD file, 2021-09-22]
scara_CAD/manipulator/35t_htd.SLDPRT
58.7 x 12.5 x 58.7 mm
