signalben/Planar-Grasping-Platform/scara_CAD/manipulator/nema23_long.SLDPRT

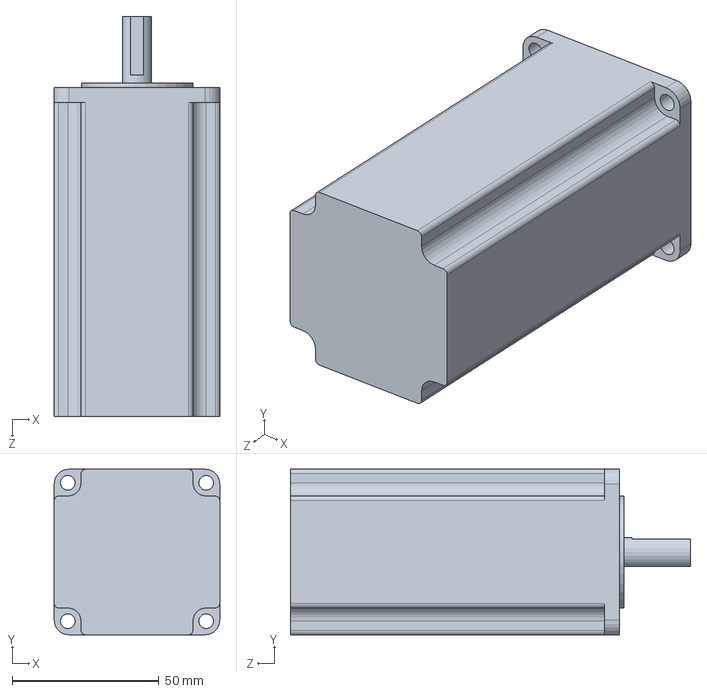
[picture p80: CAD file, 2021-09-22]
scara_CAD/manipulator/nema23_long.SLDPRT
56.4 x 56.4 x 136.2 mm
