signalben/Planar-Grasping-Platform/scara_CAD/manipulator/j3top.SLDPRT

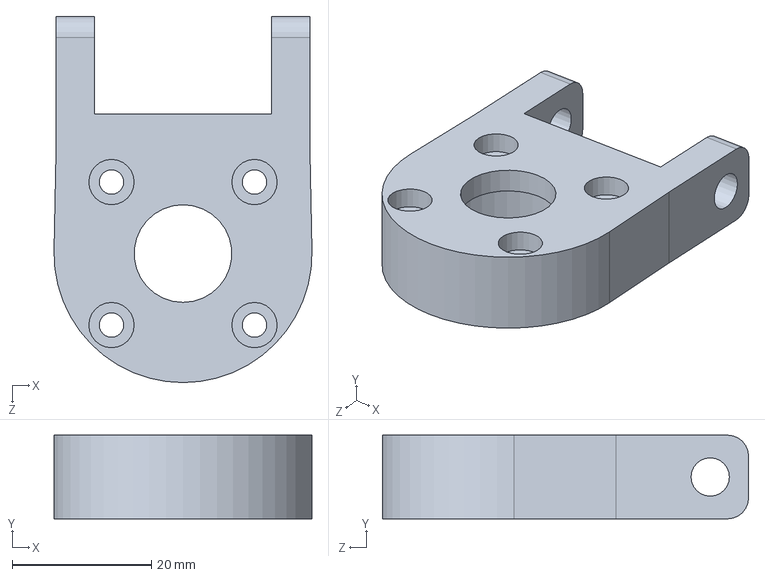
[picture p81: CAD file, 2021-09-22]
scara_CAD/manipulator/j3top.SLDPRT
37.0 x 12.0 x 52.5 mm
