signalben/Planar-Grasping-Platform/scara_CAD/manipulator/70t_htd.SLDPRT

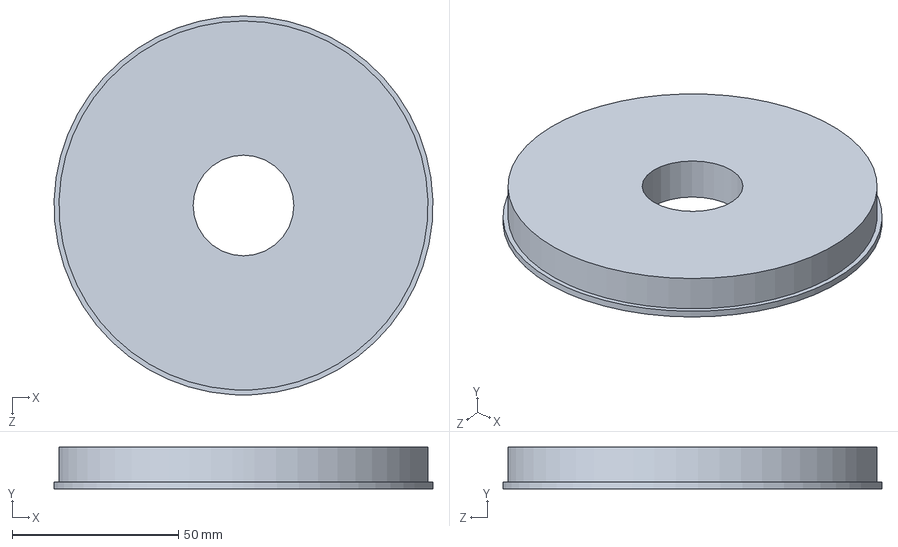
[picture p82: CAD file, 2021-09-22]
scara_CAD/manipulator/70t_htd.SLDPRT
113.9 x 12.5 x 114.0 mm
