signalben/Planar-Grasping-Platform/scara_CAD/manipulator/shaft2.SLDPRT

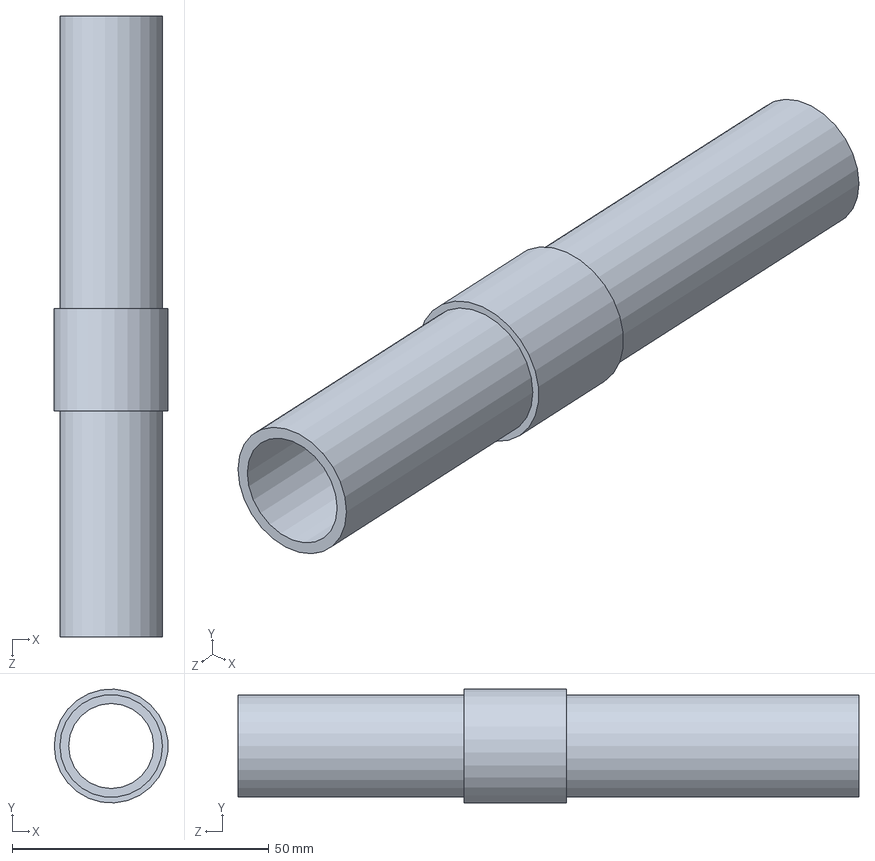
[picture p83: CAD file, 2021-09-22]
scara_CAD/manipulator/shaft2.SLDPRT
22.1 x 22.2 x 121.0 mm
