signalben/Planar-Grasping-Platform/scara_CAD/manipulator/linear_carriage.SLDPRT

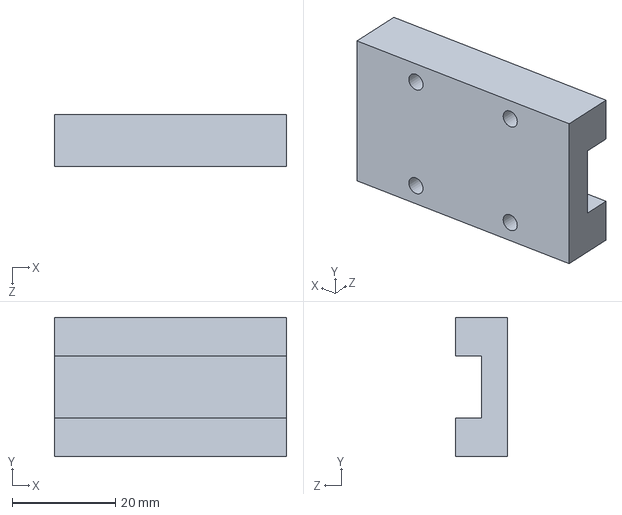
[picture p84: CAD file, 2021-09-22]
scara_CAD/manipulator/linear_carriage.SLDPRT
45.0 x 27.0 x 10.0 mm
