signalben/Planar-Grasping-Platform/scara_CAD/manipulator/buttress.SLDPRT

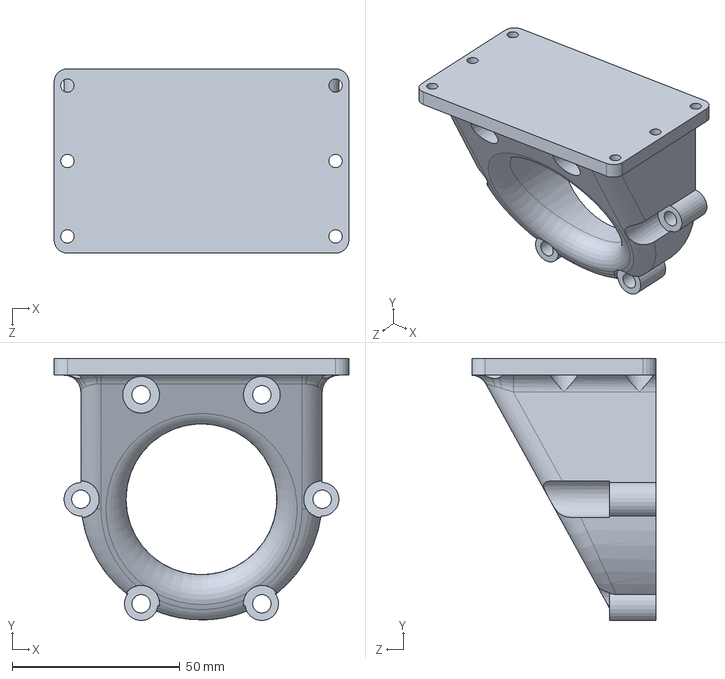
[picture p85: CAD file, 2021-09-22]
scara_CAD/manipulator/buttress.SLDPRT
88.0 x 78.2 x 55.0 mm
