signalben/Planar-Grasping-Platform/scara_CAD/manipulator/retainer.SLDPRT

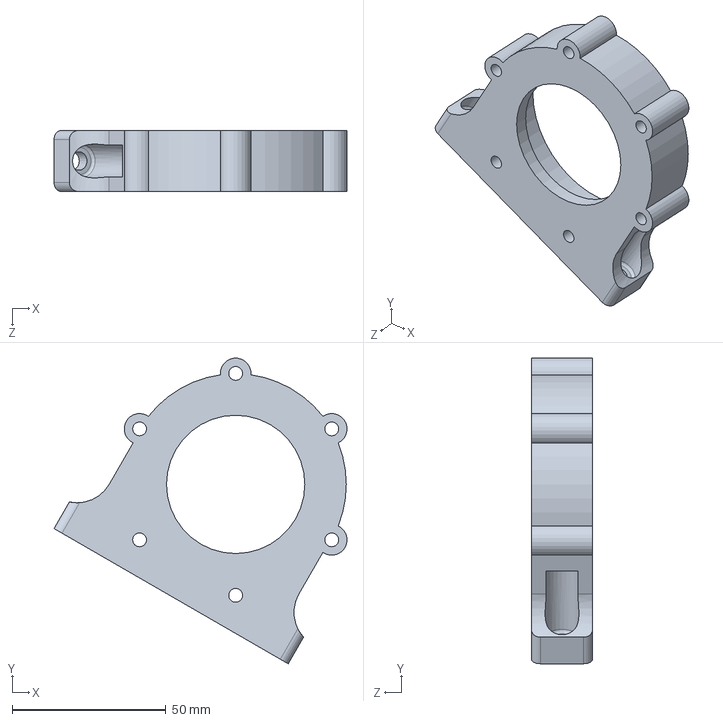
[picture p86: CAD file, 2021-09-22]
scara_CAD/manipulator/retainer.SLDPRT
95.3 x 99.4 x 20.0 mm
