signalben/Planar-Grasping-Platform/scara_CAD/manipulator/j3top2.SLDPRT

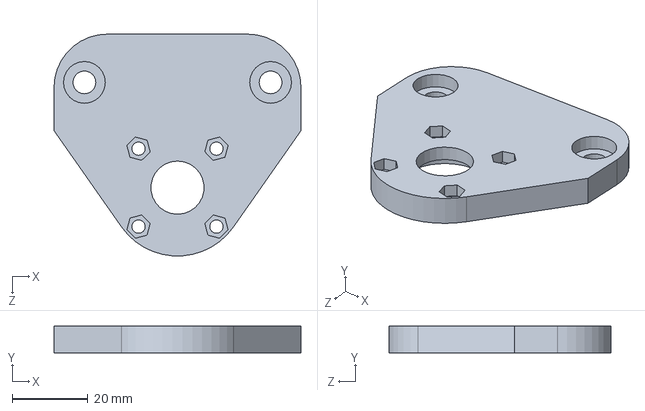
[picture p87: CAD file, 2021-09-22]
scara_CAD/manipulator/j3top2.SLDPRT
65.0 x 7.00 x 58.4 mm
