signalben/Planar-Grasping-Platform/scara_CAD/manipulator/retainer_basic.SLDPRT

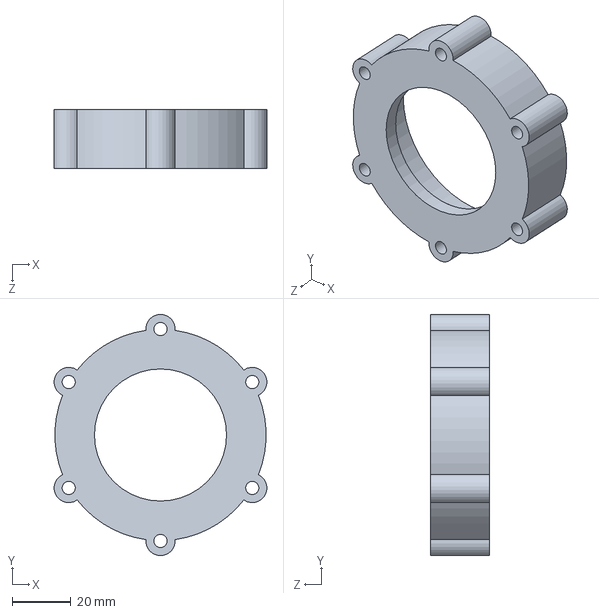
[picture p88: CAD file, 2021-09-22]
scara_CAD/manipulator/retainer_basic.SLDPRT
72.5 x 82.1 x 20.0 mm
