signalben/Planar-Grasping-Platform/scara_CAD/manipulator/ballnut.SLDPRT

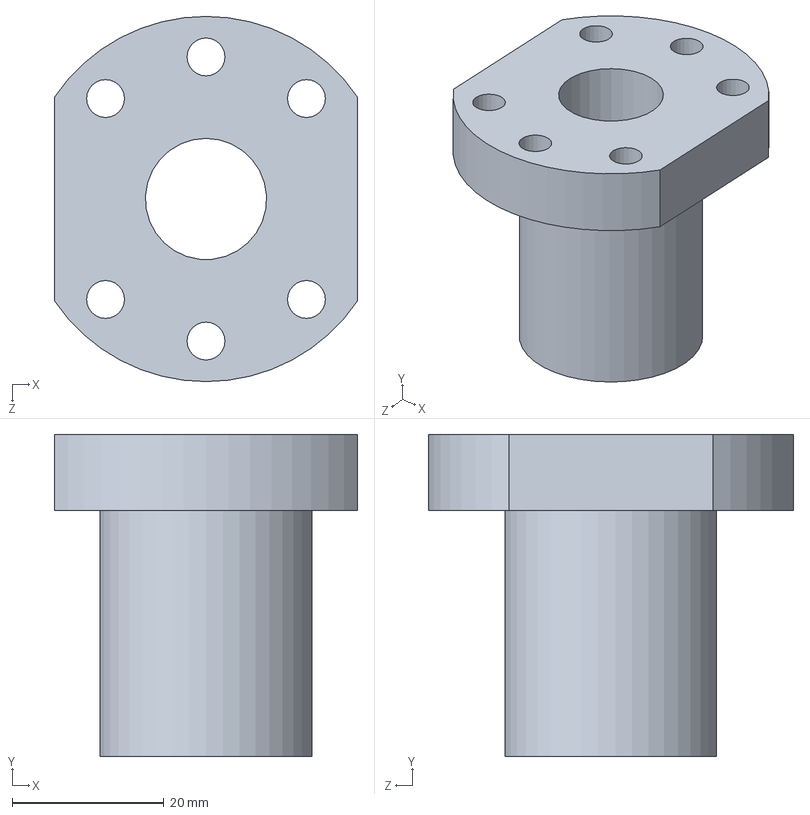
[picture p89: CAD file, 2021-09-22]
scara_CAD/manipulator/ballnut.SLDPRT
40.0 x 42.5 x 48.2 mm
