signalben/Planar-Grasping-Platform/scara_CAD/manipulator/ally_plate1.SLDPRT

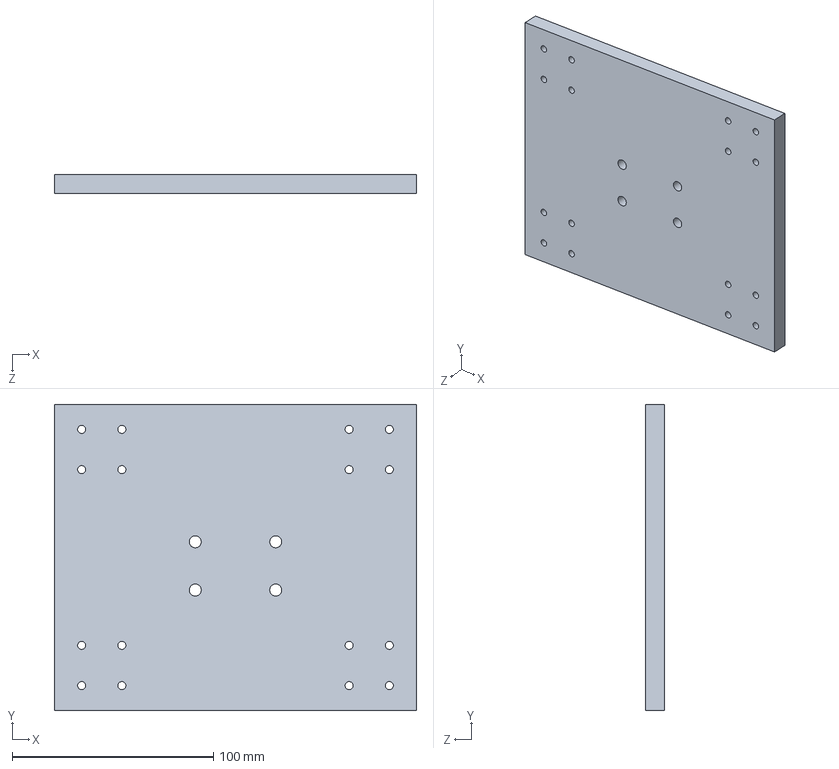
[picture p90: CAD file, 2021-09-22]
scara_CAD/manipulator/ally_plate1.SLDPRT
180.0 x 152.4 x 9.50 mm
