signalben/Planar-Grasping-Platform/scara_CAD/manipulator/linear_rail.SLDPRT

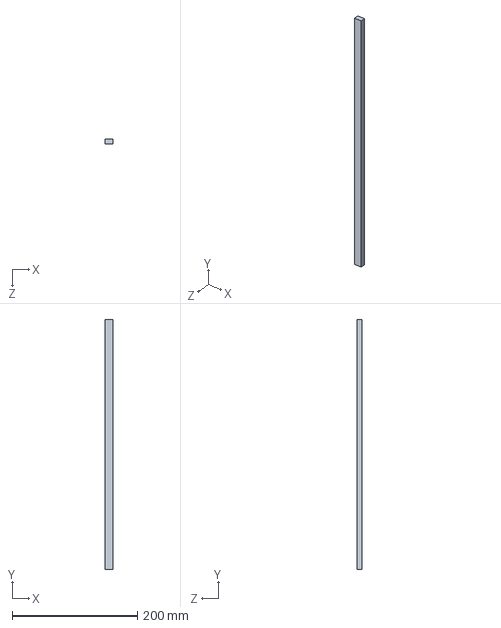
[picture p91: CAD file, 2021-09-22]
scara_CAD/manipulator/linear_rail.SLDPRT
12.0 x 400.0 x 8.00 mm
