signalben/Planar-Grasping-Platform/scara_CAD/manipulator/ally_bar.SLDPRT

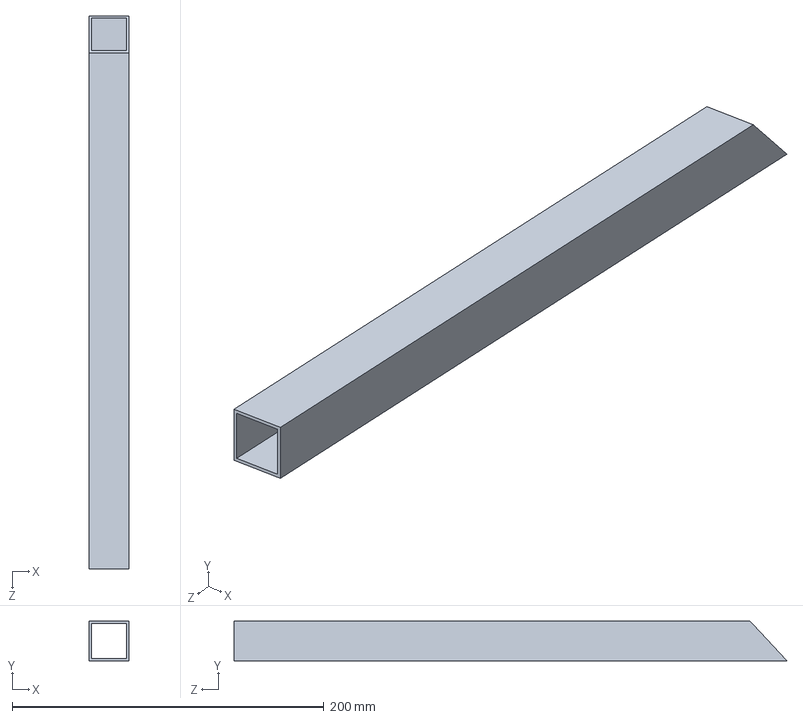
[picture p92: CAD file, 2021-09-22]
scara_CAD/manipulator/ally_bar.SLDPRT
25.4 x 25.4 x 355.0 mm
