signalben/Planar-Grasping-Platform/scara_CAD/manipulator/smallshaft.SLDPRT

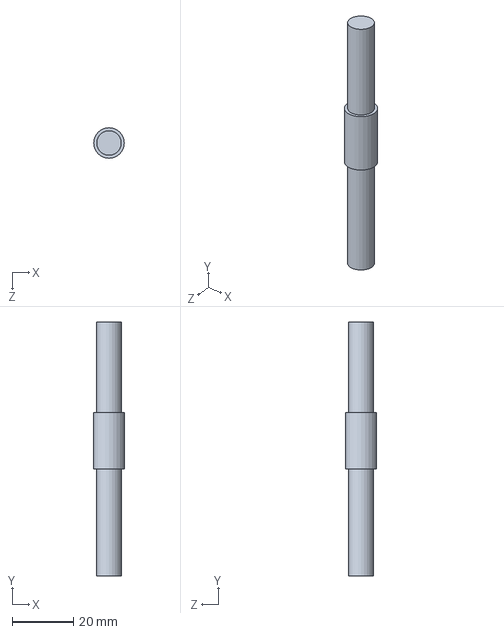
[picture p93: CAD file, 2021-09-22]
scara_CAD/manipulator/smallshaft.SLDPRT
10.0 x 82.9 x 10.0 mm
