signalben/Planar-Grasping-Platform/scara_CAD/manipulator/top_plate.SLDPRT

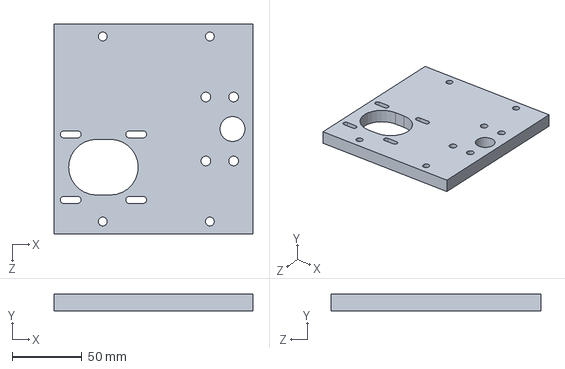
[picture p94: CAD file, 2021-09-22]
scara_CAD/manipulator/top_plate.SLDPRT
143.1 x 12.0 x 151.0 mm
