signalben/Planar-Grasping-Platform/scara_CAD/manipulator/ally_bar_12.SLDPRT

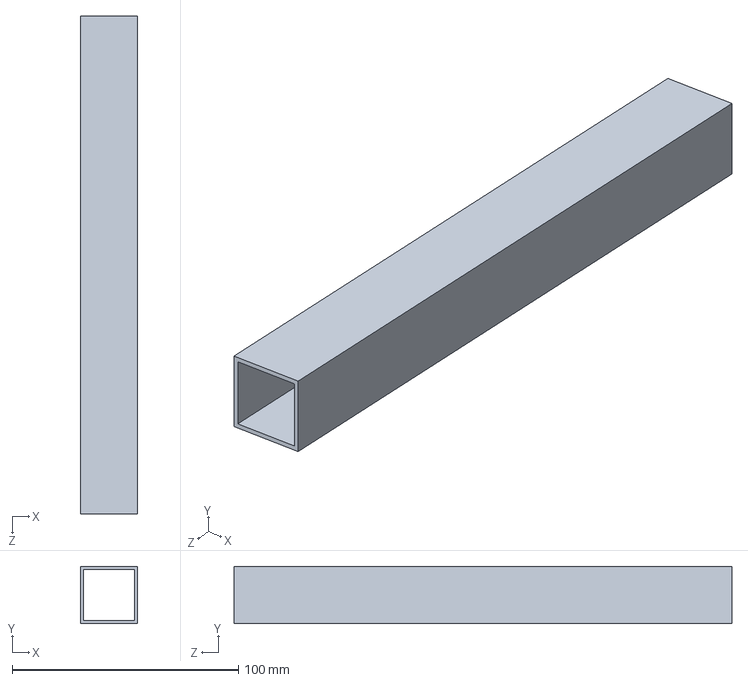
[picture p95: CAD file, 2021-09-22]
scara_CAD/manipulator/ally_bar_12.SLDPRT
25.4 x 25.4 x 220.0 mm
